MichaelRColton/PSDR/Hardware/Block_Diagram/Block Diagram.png

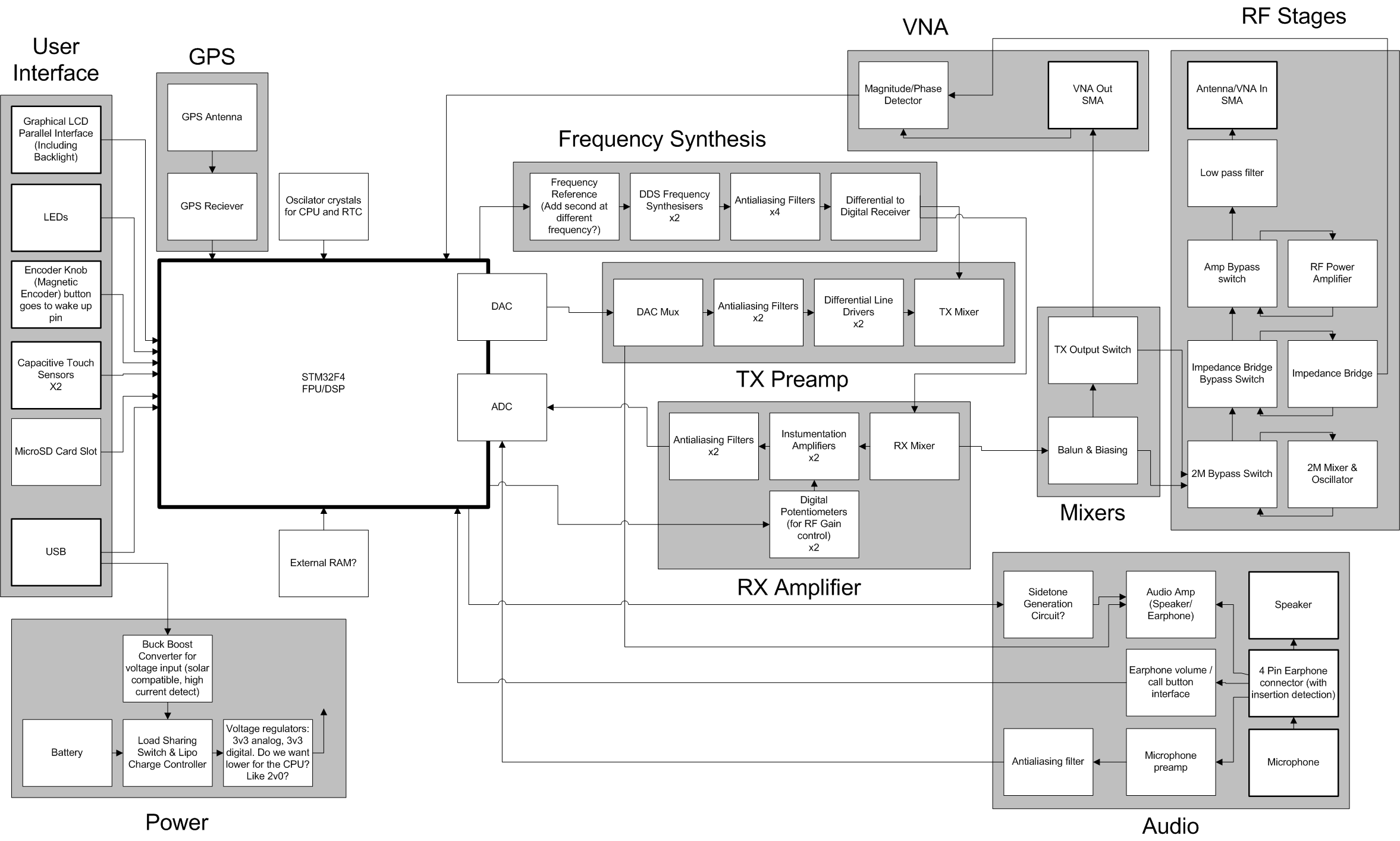
Hardware/Block_Diagram/Block Diagram.png
