MichaelRColton/PSDR/Hardware/Gerbers/PSDR1/bottom.png

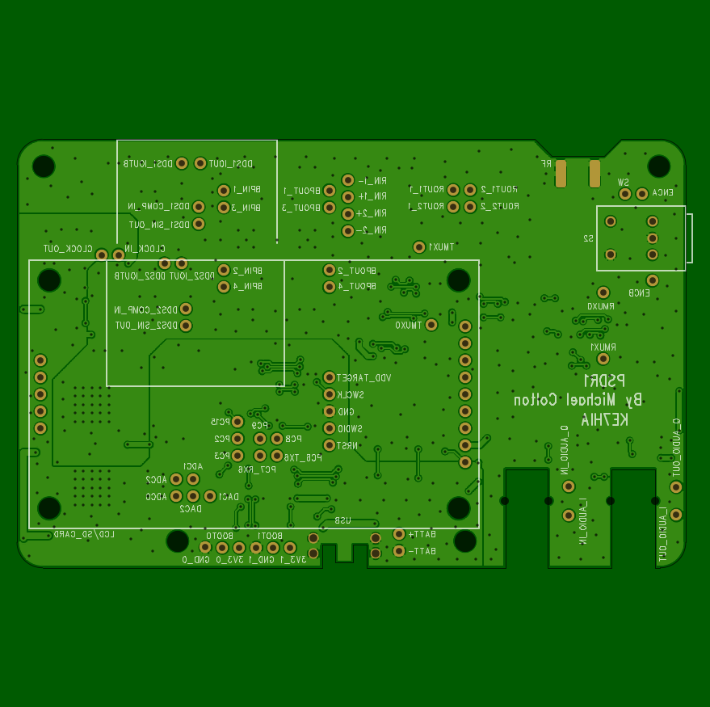
Hardware/Gerbers/PSDR1/bottom.png
