MichaelRColton/PSDR/Hardware/Gerbers/PSDR1/top.png

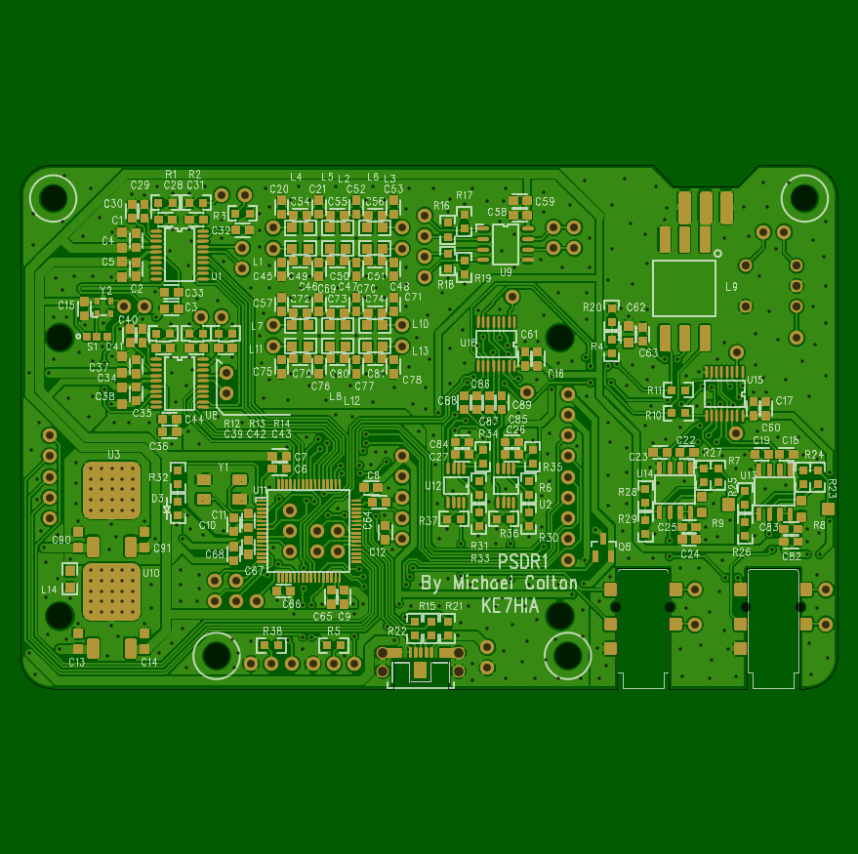
Hardware/Gerbers/PSDR1/top.png
