MichaelRColton/PSDR/Hardware/Gerbers/PSDR2 Encoder Board/BOTTOM.png

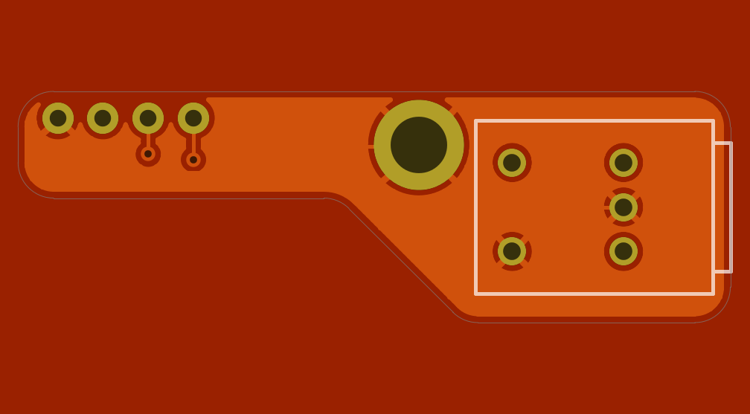
Hardware/Gerbers/PSDR2 Encoder Board/BOTTOM.png
