MichaelRColton/PSDR/Hardware/Gerbers/PSDR2 Encoder Board/TOP.png

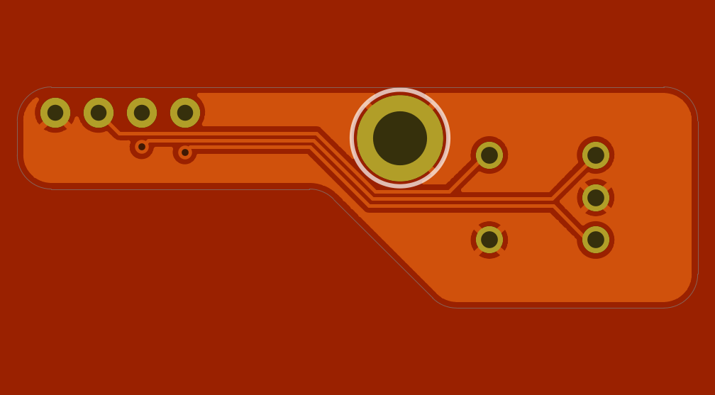
Hardware/Gerbers/PSDR2 Encoder Board/TOP.png
