MichaelRColton/PSDR/Hardware/Gerbers/PSDR2 Main Board/ALL_COPPER.png

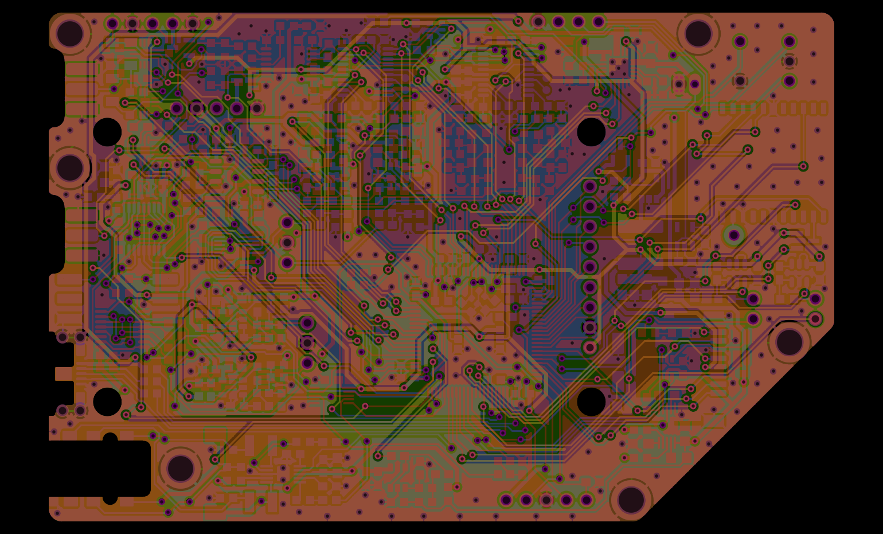
Hardware/Gerbers/PSDR2 Main Board/ALL_COPPER.png
