MichaelRColton/PSDR/Hardware/Gerbers/PSDR2 Main Board/bottom.png

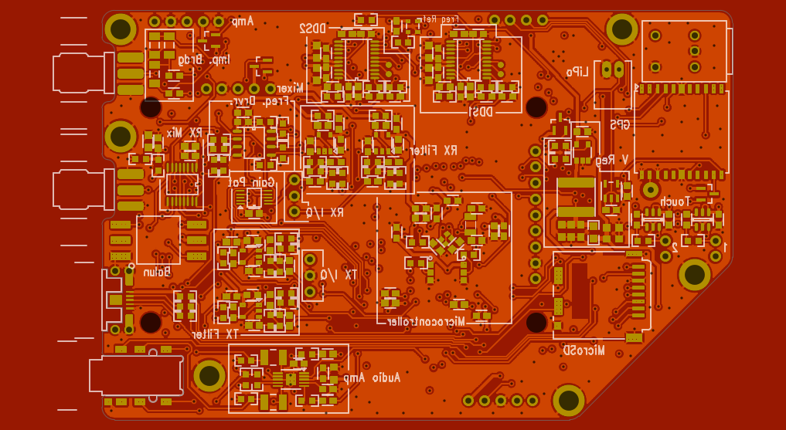
Hardware/Gerbers/PSDR2 Main Board/bottom.png
