MichaelRColton/PSDR/Hardware/Gerbers/PSDR2 Main Board/top.png

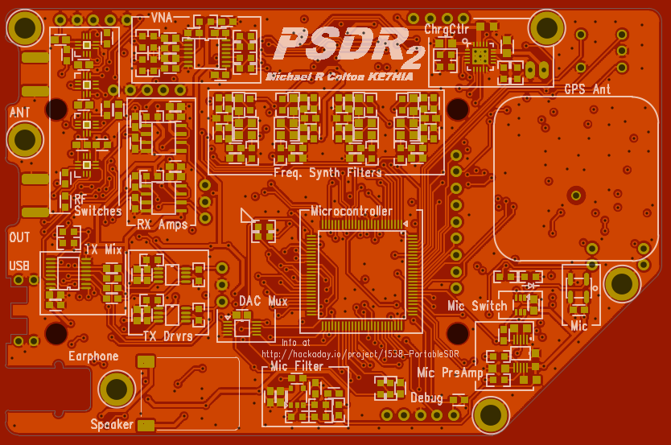
Hardware/Gerbers/PSDR2 Main Board/top.png
