MichaelRColton/PSDR/Hardware/Gerbers/PSDR25 Main Board/TOP.png

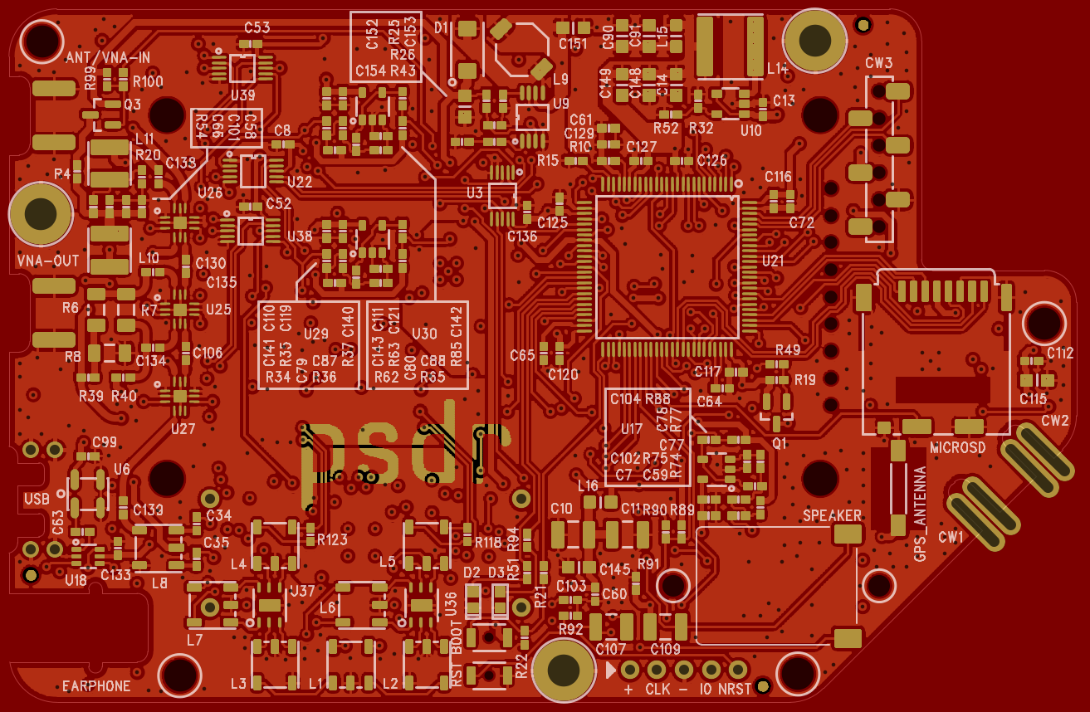
Hardware/Gerbers/PSDR25 Main Board/TOP.png
