MichaelRColton/PSDR/Hardware/Gerbers/PSDR25_Encoder Board/BOTTOM.png

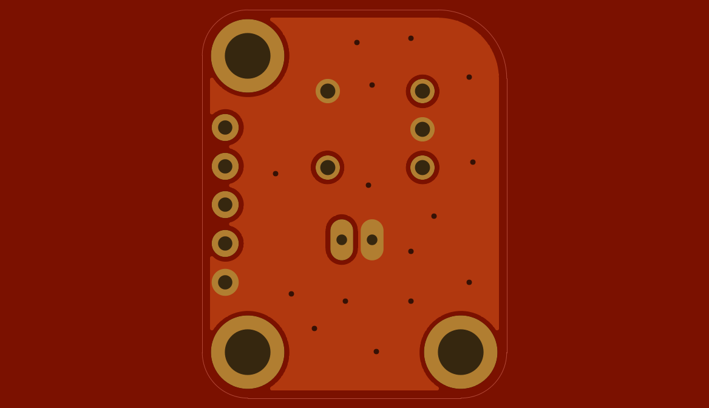
Hardware/Gerbers/PSDR25_Encoder Board/BOTTOM.png
