MichaelRColton/PSDR/Keychain/Gerbers/BOTTOM.png

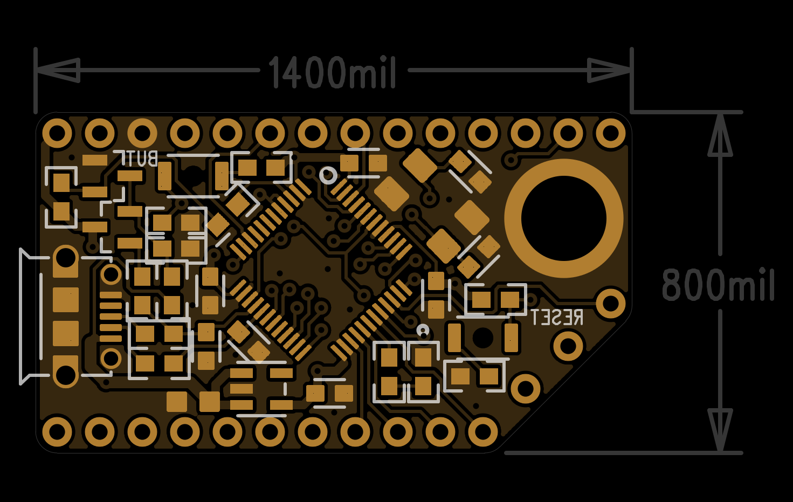
Keychain/Gerbers/BOTTOM.png
