MichaelRColton/PSDR/Keychain/Gerbers/PSDR_Keychain.png

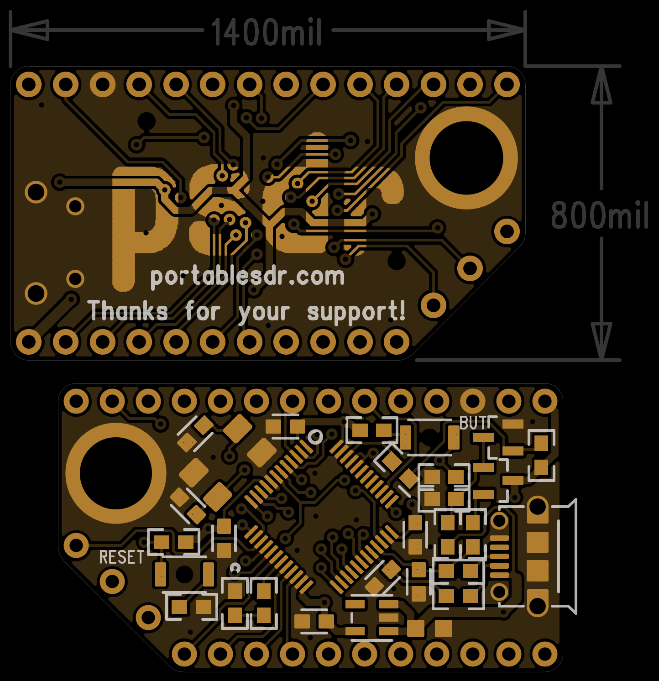
Keychain/Gerbers/PSDR_Keychain.png
