MichaelRColton/PSDR/Keychain/Gerbers/TOP.png

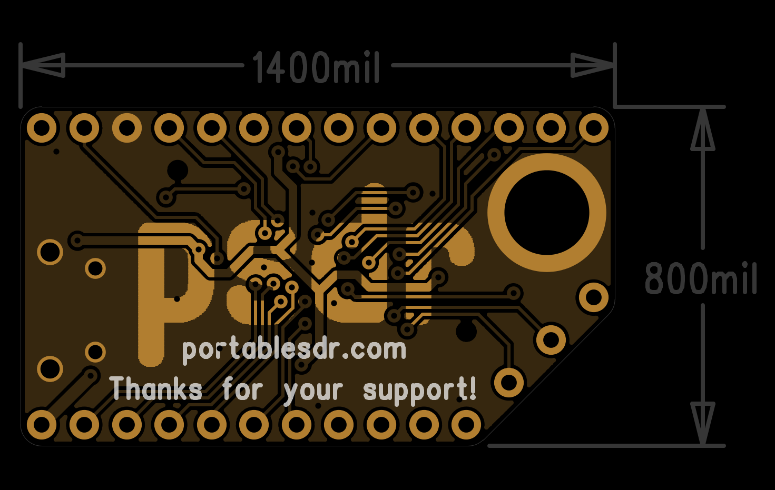
Keychain/Gerbers/TOP.png
