MichaelRColton/PSDR/Hardware/BOMs/PSDR_2.0.0/PSDR2_BOM_Simple.xlsx

RefDes | Count | Part Type | Value | Vendor Part No. | Mfg | Mfg Part No. | Substitutions?
L14 | 1 | 2U2H_INDUCTOR_NR6028T2R2N |  | 587-2098-1-ND | Taiyo Yuden | NR6028T2R2N | Yes
EARPHONE | 1 | 3.5MM_PHONO_4P_3SW_SJ-42617-SMT |  | CP-43617SJCT-ND | CUI Inc | SJ-43617-SMT-TR | No
U11 | 1 | 3V3_LDO_MCP1802 |  | MCP1802T-3302I/OTCT-ND | Microchip Technology | MCP1802T-3302I/OT | No
U15, 16 | 2 | 74CBTLV3253 |  | 568-5265-1-ND | NXP Semiconductors | 74CBTLV3253DS,118 | No
Y2 | 1 | 75MHZ_OSC |  | 535-11201-1-ND | Abracon Corporation | ASDMB-75.000MHZ-LY-T | No
U2, 12 | 2 | AD8131 |  | AD8131ARMZ-ND | Analog Devices Inc | AD8131ARMZ-REEL7 | No
U23 | 1 | AD8302 |  | AD8302ARUZ-ND | Analog Devices Inc | AD8302ARUZ | No
U1, 8 | 2 | AD9834 |  | AD9834CRUZ-ND | Analog Devices Inc | AD9834CRUZ | No
U6 | 1 | ALT-MICROPHONE_MEMS_SPU0410HR5H-PB |  | 423-1138-1-ND | Knowles | SPU0410HR5H-PB | No
U28 | 1 | AUDIO_AMP_TPA0253DGQR |  | 296-7006-1-ND | Texas Instruments | TPA0253DGQR | No
U7 | 1 | BAT-MANAGE_MCP73871 |  | MCP73871-2AAI/ML-ND | Microchip Technology | MCP73871-2AAI/ML | No
U10 | 1 | BUCK_REGULATOR_AP3417C |  | AP3417CKTR-G1DICT-ND | Diodes Incorporated | AP3417CKTR-G1 | No
U19, 20 | 2 | CAP_SENSE_AT42QT1010 |  | AT42QT1011-TSHRCT-ND | Atmel | AT42QT1011-TSHR | No
Y1 | 1 | CRYSTAL_24MHZ_P79E |  | 490-5575-1-ND | Murata Electronics North America | XRCGB24M000F0L00R0 | No
Y5 | 1 | CRYSTAL_SMT_32.768 |  | 535-11937-1-ND | Abracon Corporation | ABS07-120-32.768KHZ-T | No
C9 | 1 | CSM-C0G-100P-5P-50V-0603 | 100p | 1276-1008-1-ND | Samsung Electro-Mechanics America, Inc | CL10C101JB8NNNC | Yes
C68, 111 | 2 | CSM-C0G-100P-5P-50V-0603 | OPEN
C50, 55, 73, 80, 121, 122 | 6 | CSM-C0G-10P-5P-50V-0603 | 6p | 1276-2133-1-ND | Samsung Electro-Mechanics America, Inc | CL10C060CB8NNNC | Yes
C123, 124 | 2 | CSM-C0G-10P-5P-50V-0603 | 8p | 1276-2140-1-ND | Samsung Electro-Mechanics America, Inc | CL10C080DB8NCNC | Yes
C31, 32, 42, 43 | 4 | CSM-C0G-18P-5P-50V-0603 | 18p | 1276-2210-1-ND | Samsung Electro-Mechanics America, Inc | CL10C180JC8NNNC | Yes
C49, 54, 72, 79 | 4 | CSM-C0G-18P-5P-50V-0603 | 1p | 1276-1293-1-ND | Samsung Electro-Mechanics America, Inc | CL10C010CB8NNNC | Yes
C20, 45, 47, 48, 52, 53, 57, 70, 71, 75, 77, 78 | 12 | CSM-C0G-18P-5P-50V-0603 | 22p | 1276-1023-1-ND | Samsung Electro-Mechanics America, Inc | CL10C220JB8NNNC | Yes
C21, 46, 69, 76 | 4 | CSM-C0G-18P-5P-50V-0603 | 33p | 1276-1070-1-ND | Samsung Electro-Mechanics America, Inc | CL10C330JB8NNNC | Yes
C51, 56, 74, 81 | 4 | CSM-C0G-18P-5P-50V-0603 | 5p | 1276-1294-1-ND | Samsung Electro-Mechanics America, Inc | CL10C050CB8NNNC | Yes
C115, 116 | 2 | CSM-C0G-3N3-5P-50V-0603 | 2n2 | 1276-1992-1-ND | Samsung Electro-Mechanics America, Inc | CL10B222KB8SFNC | Yes
C14, 90, 91, 148, 149, 4, 5, 37, 38, 92, 95-98, 145, 84, 85 | 17 | CSM-X5R-10U0-10P-10V-0805 (all but 84,85, close enough) | 10u0 | 1276-1113-1-ND | Samsung Electro-Mechanics America, Inc | CL21B106KQQNNNE | Yes
C86-89 | 4 | CSM-X5R-10U0-20P-6V3-0603 | 22u | 1276-1193-1-ND | Samsung Electro-Mechanics America, Inc | CL10A226MQ8NRNC | Yes
C16, 17, 33, 44, 108, 132, 6, 7, 143 | 9 | CSM-X5R-1U0-10P-25V-0603 | 1u0 | 1276-1946-1-ND | Samsung Electro-Mechanics America, Inc | CL10B105KP8NNNC | Yes
C107, 109 | 2 | CSM-X5R-22U-20P-10V-1210 | 220u | 1276-3375-1-ND | Samsung Electro-Mechanics America, Inc | CL32A227MQVNNNE | Yes
C24, 82, 119, 125 | 4 | CSM-X5R-2U2-10P-6V3-0603 | 2u2 | 1276-1134-1-ND | Samsung Electro-Mechanics America, Inc | CL10B225KP8NNNC | Yes
C62 | 1 | CSM-X5R-47U-20P-6V3-0805 | 47u | 1276-2420-1-ND | Samsung Electro-Mechanics America, Inc | CL21A476MQCLRNC | Yes
C13, 118, 93, 94 | 4 | CSM-X5R-4U7-10P-10V-0603 | 4u7 | 490-3297-1-ND | Murata Electronics North America | GRM188R60J475KE19D | Yes
C105, 110, 144, 146 | 4 | CSM-X5R-4U7-10P-6V3-0603 | 470n | 1276-1062-1-ND | Samsung Electro-Mechanics America, Inc | CL10B474KO8NNNC | Yes
C1-3, 8, 10-12, 25-29, 34-36, 39, 40, 59-61, 63, 83, 99, 104, 106, 112-114, 117, 120, 126-131, 133-142, 147, 150, 155, 156, 161, 162, 167, 168, 173, 174 | 56 | CSM-X7R-100N-10P-25V-0603 | 100n | 490-1532-1-ND | Murata Electronics North America | GRM188R71C104KA01D | Yes
C15, 18, 19, 22, 23, 30, 41, 58, 102, 153, 159, 165, 171 | 13 | CSM-X7R-10N-10P-50V-0603 | 10n | 490-1512-1-ND | Murata Electronics North America | GRM188R71H103KA01D | Yes
C64-67, 100, 101, 151, 152, 157, 158, 163, 164, 169, 170 | 14 | CSM-X7R-1N-10P-50V-0603 | 1n | 490-1494-1-ND | Murata Electronics North America | GRM188R71H102KA01D | Yes
C103, 154, 160, 166, 172 | 5 | CSM-X7R-1U0-10P-10V-0603 | 6u8 | 445-14209-1-ND | TDK Corporation | C1608X6S1A685K080AC | Yes
U22 | 1 | DIGITAL_POT_MAX5388 |  | MAX5388NAUB+-ND | Maxim Integrated | MAX5388NAUB+ | No
U3 | 1 | DPDT_ANALOG_MAX4525 |  | MAX4525CUB+-ND | Maxim Integrated | MAX4525CUB+ | No
U9 | 1 | DS90LV028 |  | DS90LV028AHM/NOPB-ND | Texas Instruments | DS90LV028AHM/NOPB | No
S2 | 1 | ENCODER_PEC09-2320F-S0015 |  | PEC09-2320F-S0015-ND | Bourns Inc. | PEC09-2320F-S0015 | No
U4 | 1 | GP39-1513 |  | GP39-1513 or GP-3363 or one of the new ones. GP39-1513 is the one I liked best for the Gun Box. Let's use that one. | adh-tech.com.tw | GP39-1513 | No (but see note to left)
GPS_ANT | 1 | GPS_CERAMIC_ANT_25X25X2 |  | 535-11938-ND | Abracon Corporation | APAE1575R2520ABDD7-T | Yes, physical match.
L15 | 1 | ISM-0805-10U | 10u | 535-10520-1-ND | Abracon Corporation | AISC-0805F-100J-T | Yes
L2, 3, 5, 6, 8, 10, 12, 13 | 8 | ISM-0805-10U | 390nH | 535-10508-1-ND | Abracon Corporation | AISC-0805-R39J-T | Yes
L1, 4, 7, 11 | 4 | ISM-0805-10U | 470nH | 535-10509-1-ND | Abracon Corporation | AISC-0805-R47J-T | Yes
LIPO | 1 | JST_2P_2MM |  | 455-1719-ND | JST Sales America Inc | S2B-PH-K-S(LF)(SN) | Yes
D3 | 1 | LED-WHITE-0603 | APTD1608QWF | 475-2831-1-ND | OSRAM Opto Semiconductors Inc | LW Q38E-Q1S2-3K6L-1 | Yes
U13, 14 | 2 | MCP6N11 |  | MCP6N11-010E/SN-ND | Microchip Technology | MCP6N11-010E/SN | No | OTHER GAIN OPTIONS EXIST (the -010 part) I should try them.
U5 | 1 | MIC_PREAMP_SSM2167 |  | SSM2167-1RMZ-R7CT-ND | Analog Devices Inc | SSM2167-1RMZ-R7 | No
MICROSD | 1 | MICROSD_DM3CS-SF |  | DM3CS-SF | Hirose Electric Co Ltd | DM3CS-SF | No
USB | 1 | MICROUSB_H12192CT-ND |  | H12192CT-ND | Hirose Electric Co Ltd | ZX62WRD-B-5PC | No
Q1-3, 8 | 4 | MOSFET_P_SOT23_IRLML6401 |  | IRLML6401PBFCT-ND | International Rectifier | IRLML6401TRPBF | Yes
U17, 29-32 | 5 | OP_AMP_FAN4174 |  | FAN4174IS5XCT-ND | Fairchild Semiconductor | FAN4174IS5X | No
LCD | 1 | QVGA_SPI_DISPLAY_MINIMAL |  |  | ebay (also alibaba) |  | Yes | Supplier TBD
U24-27 | 4 | RF_DPDT_MASWSS0129TR |  | 1465-1374-1-ND | M/A-Com Technology Solutions | MASWSS0129TR-3000 | No
R5, 21, 28-31, 33, 55, 78-89 | 20 | RSM-0R0-1PCT-125MW-0603 | 0R0 | 541-0.0GCT-ND | Vishay Dale | CRCW06030000Z0EA | Yes
R49, 50, 56, 57, 60, 64, 65, 68, 69, 72, 73, 76, 77, 90-95 | 19 | RSM-100K-1PCT-100MW-0603 | 100K | P100KGCT-ND | Panasonic Electronic Components | ERJ-3GEYJ104V | Yes
R43 | 1 | RSM-100R-1PCT-100MW-0603 | 100R | P100GCT-ND | Panasonic Electronic Components | ERJ-3GEYJ101V | Yes
R4, 20, 44, 45, 47, 48, 62, 63, 66, 67, 70, 71, 74, 75 | 14 | RSM-10K0-1PCT-100MW-0603 | 10K0 | MCT0603-10.0K-CFCT-ND | Vishay Beyschlag | MCT06030C1002FP500 | Yes
R41 | 1 | RSM-10K0-1PCT-100MW-0603 | 10K0 NTC | 490-2436-1-ND | Murata Electronics North America | NCP18XH103J03RB | Yes
R39 | 1 | RSM-110K-1PCT-100MW-0603 | 110K | P110KGCT-ND | Panasonic Electronic Components | ERJ-3GEYJ114V | Yes
R51, 52, 96, 97 | 4 | RSM-12K1-1PCT-100MW-0603 | 12K1 | 1276-4751-1-ND | Samsung Electro-Mechanics America, Inc | RC1608F1212CS | Yes
R10, 11 | 2 | RSM-150R-1PCT-100MW-0603 | 150R | P150GCT-ND | Panasonic Electronic Components | ERJ-3GEYJ151V | Yes
R38 | 1 | RSM-15K0-1PCT-100MW-0603 | 15K0 | MCT0603-15.0K-CFCT-ND | Vishay Beyschlag | MCT06030C1502FP500 | Yes
R9, 23, 24, 27, 46, 58, 59 | 7 | RSM-1K00-1PCT-100MW-0603 | 1K00 | MCT0603-1.00K-CFCT-ND | Vishay Beyschlag | MCT06030C1001FP500 | Yes
R42 | 1 | RSM-1K30-1PCT-100MW-0603 | 1K30 | 311-1.3KGRCT-ND | Yageo | RC0603JR-071K3L | Yes
R2, 3, 13, 14, 16, 17, 18, 19 | 8 | RSM-200R-1PCT-100MW-0603 | 200R | P200HCT-ND | Panasonic Electronic Components | ERJ-3EKF2000V | Yes
R53, 54 | 2 | RSM-22K1-1PCT-100MW-0603 | 22K1 | P22.1KHCT-ND | Panasonic Electronic Components | ERJ-3EKF2212V | Yes
R15, 22 | 2 | RSM-22R1-1PCT-100MW-0603 | 22R1 | 1276-3497-1-ND | Samsung Electro-Mechanics America, Inc | RC1608F22R1CS | Yes
R34, 35 | 2 | RSM-24R9-1PCT-100MW-0603 | 24R9 | 1276-3499-1-ND | Samsung Electro-Mechanics America, Inc | RC1608F24R9CS | Yes
R32 | 1 | RSM-255R-1PCT-100MW-0603 | 255R | P255HCT-ND | Panasonic Electronic Components | ERJ-3EKF2550V | Yes
R40 | 1 | RSM-332K-1PCT-100MW-0603 | 332K | P332KHCT-ND | Panasonic Electronic Components | ERJ-3EKF3323V | Yes
R61 | 1 | RSM-383K-1PCT-100MW-0603 | 383K | P383KHCT-ND | Panasonic Electronic Components | ERJ-3EKF3833V | Yes
R25, 26, 36, 37 | 4 | RSM-49R9-1PCT-100MW-0603 | 49R9 | 1276-3505-1-ND | Samsung Electro-Mechanics America, Inc | RC1608F49R9CS | Yes
R1, 12 | 2 | RSM-6K81-1PCT-100MW-0603 | 6K81 | P6.81KHCT-ND | Panasonic Electronic Components | ERJ-3EKF6811V | Yes
R6, 7, 8 | 3 | RSM-6K98-1PCT-250MW-1206 | 50R (49R9) | P49.9FCT-ND | Panasonic Electronic Components | ERJ-8ENF49R9V | Yes
ANT/VNA-IN, VNA-OUT | 2 | SMA_BOARD_EDGE |  | J629-ND | Cinch Connectivity Solutions Johnson | 142-0711-821 | Yes (Physical Match Required)
U18 | 1 | SPDT_ANALOG_SWITCH_SN74LVC1G3157 |  | 296-14909-1-ND | Texas Instruments | SN74LVC1G3157DCKR | No
SPEAKER | 1 | SPEAKER_SMT_WATERPROOF_2403-260-00107 |  | 423-1203-ND | Knowles | 2403 260 00107 | Maybe
U21 | 1 | STM32F429_LQFP100 |  | 497-14052-ND | STMicroelectronics | STM32F429VIT6 | Yes, ST, pin compatible, equal or higher specs.
L9 | 1 | T4-1-KK81 |  |  | Mini-Circuits | T4-1-KK81 | No
 | 0.3 | LCD Male Header |  | SAM1000-32-ND | Samtec Inc | BBL-132-G-E | Yes. See below
 | 0.3 | LCD Female Header |  | SAM1104-32-ND | Samtec Inc | BBL-132-G-E | Yes. Must mate with above, stacked height may not change
 | 1.00 | Lipo |  |  | Sparkfun.com | PRT-08483
Number of different parts | 85
Part count | 337.6
