MichaelRColton/PSDR/Hardware/BOMs/PSDR_1.0.0/PSDR1_BOM.xlsx

RefDes | Count | Part Type | Mfg PN | Vendor PN | Manufacturer | Value
C1-3,6,8,9,12,25-29,34-36,39,40,59-61,63,66,67,83 | 24 | CSM-X7R-100N-10P-25V-0603 |  | 490-1532-1-ND |  | 100n
C15,18,19,22,23,30,41,58 | 8 | CSM-X7R-10N-10P-50V-0603 |  | 490-1512-1-ND |  | 10n
C4,5,37,38,13,14,84,85,90,91 | 10 | CSM-X5R-10U0-10P-25V-0805 |  | 1276-1113-1-ND |  | 10u0
C10,11,31,32,42,43 | 6 | CSM-C0G-18P-5P-50V-0603 |  | 1276-2210-1-ND |  | 18p
C49,54,72,79 | 4 | CSM-C0G-18P-5P-50V-0603 |  | 1276-1293-1-ND |  | 1p
C16,17,33,44,68 | 5 | CSM-X5R-1U0-10P-25V-0603 |  | 1276-1946-1-ND |  | 1u0
C20,45,47,48,52,53,57,70,71,75,77,78 | 12 | CSM-C0G-18P-5P-50V-0603 |  | 1276-1023-1-ND |  | 22p
C24,64,65,82 | 4 | CSM-X5R-2U2-10P-6V3-0603 |  | 1276-1134-1-ND |  | 2u2
C21,46,69,76 | 4 | CSM-C0G-18P-5P-50V-0603 |  | 1276-1070-1-ND |  | 33p
C62 | 1 | CSM-X5R-47U-20P-6V3-0805 |  | 1276-2420-1-ND |  | 47u
C7 | 1 | CSM-X5R-4U7-10P-10V-0603 |  | 1276-2087-1-ND |  | 4u7
C51,56,74,81 | 4 | CSM-C0G-18P-5P-50V-0603 |  | 1276-1294-1-ND |  | 5p
C50,55,73,80 | 4 | CSM-C0G-18P-5P-50V-0603 |  | 1276-2133-1-ND |  | 6p
C86-89 | 4 | CSM-X5R-10U0-20P-6V3-0603 |  | 1276-1193-1-ND |  | 22u
R8,9 | 2 | 10K_POT |  | TC33X-103ECT-ND
R21 | 1 | RSM-0R0-1PCT-125MW-0603 |  | 541-0.0GCT-ND |  | 0R0
R7,23 | 2 | RSM-100K-1PCT-100MW-0603 |  | 541-100KHCT-ND |  | 100K
R4,5,20,38 | 4 | RSM-10K0-1PCT-100MW-0603 |  | MCT0603-10.0K-CFCT-ND |  | 10K0
R10,11 | 2 | RSM-150R-1PCT-100MW-0603 |  | 541-150HCT-ND |  | 150R
R6,24-31,33 | 9 | RSM-1K00-1PCT-100MW-0603 |  | MCT0603-1.00K-CFCT-ND |  | 1K00
R2,3,13,14,16-19 | 8 | RSM-200R-1PCT-100MW-0603 |  | 541-200HCT-ND |  | 200R
R15,22 | 2 | RSM-22R1-1PCT-100MW-0603 |  | 541-22.1HCT-ND |  | 22R1
R34,35 | 2 | RSM-24R9-1PCT-100MW-0603 |  | 541-24.9HCT-ND |  | 24R9
R32 | 1 | RSM-255R-1PCT-100MW-0603 |  | 541-255HCT-ND |  | 255R
R36,37 | 2 | RSM-49R9-1PCT-100MW-0603 |  | 541-49.9HCT-ND |  | 49R9
R1,12 | 2 | RSM-6K81-1PCT-100MW-0603 |  | MCT0603-6.80K-CFCT-ND |  | 6K81
L2,3,5,6,8,10,12,13 | 8 | ISM-0805-10U |  | 535-10508-1-ND |  | 390nH
L1,4,7,11 | 4 | ISM-0805-10U |  | 535-10509-1-ND |  | 470nH
L14 | 1 | ISM-0805-10U |  | 535-10520-1-ND |  | 10u
D3 | 1 | LED-WHITE-0603 | VLMW11R2S2-5K8L-08 | VLMW11R2S2-5K8L-08CT-ND
L9 | 1 | T4-1-KK81 | T4-1-KK81+
LCD/SD_CARD | 1 | QVGA_SPI_DISPLAY
Q8 | 1 | MOSFET_P_SOT23_IRLML6401 | IRLML6401TRPBF | IRLML6401PBFCT-ND
RF | 1 | SMA_BOARD_EDGE | 142-0711-821 | J629-ND
RX_I/Q, TX_I/Q | 2 | PHONO_JACK_STEREO_CUTOUT_SWITCHES | SJ-3503-SMT-TR | CP-3503SJCT-ND
S2 | 1 | ENCODER_PEC09-2320F-S0015 | PEC09-2320F-S0015 | PEC09-2320F-S0015-ND
U1,8 | 2 | AD9834 | AD9834CRUZ-ND | AD9834CRUZ-ND
U2,12 | 2 | AD8131 | AD8131 | AD8131ARMZ-ND
U3,10 | 2 | LD39300DT33-R | LD39300DT33-R | 497-6874-1-ND
U9 | 1 | DS90LV028 | DS90LV028AHM/NOPB | DS90LV028AHM/NOPB-ND
U11 | 1 | STM32F415RG | STM32F415RG | 497-11907-ND
U13,14 | 2 | MCP6N11 | MCP6N11-010E/SN-ND | MCP6N11-010E/SN-ND
U15,16 | 2 | 74CBTLV3253 | 74CBTLV3253DS,118 | 568-5265-1-ND
USB | 1 | MICROUSB_H12192CT-ND | ZX62WRD-B-5PC | H12192CT-ND
Y1 | 1 | ABMM2-8.000MHZ-E2-T | ABMM2-8.000MHZ-E2-T | 535-9628-1-ND
Y2 | 1 | 75MHZ_OSC | ASDMB-75.000MHZ-LY-T | 535-11201-1-ND
Grand Count | 71
 | 2 | IC TOUCH SENSOR 1KEY SOT23-6 | AT42QT1011-TSHR | AT42QT1011-TSHRCT-ND | Atmel
 | 2 | 2.2nF Cap
 | 2 | 22k RES
 | 2 | 100nF Cap
 | 1 | CONN HEADER PH SIDE 2POS 2MM |  | 455-1719-ND
 | 1 | IC MCU ARM 2MB FLASH 100LQFP | STM32F429VIT6 | 497-14052-ND
 | 0 | CONN AUDIO JACK 3.5MM 4COND SMD | SJ-43516-SMT-TR | CP-43516SJCT-ND |  |  | 0.338 | watts
 | 1 | CONN JACK 3.5MM R/A 4POS MID SMD | SJ-43617-SMT-TR | CP-43617SJCT-ND
 | 1 | IC REG LDO 3.3V 0.3A SOT23-5 | MCP1802T-3302I/OT | MCP1802T-3302I/OTCT-ND |  |  |  | 2000
 | 1 | IC POT DGTL 256-TAP 10UMAX | MAX5388NAUB+ | MAX5388NAUB+-ND |  |  |  | 15.38461538
 | 4 | DPDT LEAD FREE SWITCH DC - 6GHZ | MASWSS0129TR-3000 | 1465-1374-1-ND
 | 1 | IC AMP AUDIO PWR 1W MONO 10MSOP | TPA0253DGQR | 296-7006-1-ND
 | 2 | CAP CER 220UF 6.3V 20% X5R 1210 |  | 1276-3375-1-ND
 | 1 | IC SWITCH SPDT SC70-6 |  | 296-14909-1-ND |  |  |  | 0.435
 | 1 | IC MULTIPLEXER 2X2 10UMAX |  | MAX4525CUB+-ND |  |  |  | 13.33333333
 | 1 | IC REG BUCK SYNC ADJ 1A SOT25 |  | AP3417CKTR-G1DICT-ND | These are so cheap and small, what's the catch?
 | 1 | INDUCTOR 2.2UH 4.2A 30% SMD |  | 587-2098-1-ND
