MichaelRColton/PSDR/Hardware/BOMs/PSDR_2.6.1/PSDR2.6.1_BOM.xls

 | Yellow is changed from 2.6
 | Red is something to take note of.
Item No. | Ref Des | Qty per unit | Type | Vendor | Vendor Part # | Mfg | Mfg Part # | Value |  | Cost x1 | Cost x10 | Cost x100 | Run Tot x1 | Run Tot x10 | Run Tot x100
1 | -,+,CLK,IO,NRST | 2 | 0.1"_1PIN * 5 for programming header, and encoder board | Digikey | WM50018-05-ND |  |  |  | Only One will be populated per board (give the second one to me) | 0.51 | 0.482 | 0.3693 | 1.02 | 0.964 | 0.7386
2 | ANT/VNA-IN,VNA-OUT | 2 | SMA_BOARD_EDGE | Digikey | J629-ND |  |  |  |  | 7.15 | 6.37 | 4.68 | 14.3 | 12.74 | 9.36
3 | BOOT,RST | 2 | BUTTON_B3U-1000P-B | Digikey | SW1143CT-ND |  |  |  |  | 1.25 | 1.201 | 0.9064 | 2.5 | 2.402 | 1.8128
4 | C3,10,13,17,20,21,26,27,31,33,35,36,38,40,48,49,59,60,71,73,78,80,87,88,96,111,118,119,123,129,139,157,193,209,210,212,217,218,228,229,238-240,242,243,248,256,259,265,267,269,275,277,282-284,289-295,302,303,305,306,317 | 68 | CAP_0603 | Digikey | 490-1532-1-ND |  |  | 100N |  | 0.1 | 0.019 | 0.0086 | 6.8 | 1.292 | 0.5848
5 | C9,278,281,316 | 4 | CAP_0603 | Digikey | 1276-1008-1-ND |  |  | 100p |  | 0.1 | 0.025 | 0.0116 | 0.4 | 0.1 | 0.0464
6 | C46,57,135,215,226 | 5 | CAP_0603 | Digikey | 490-1512-1-ND |  |  | 10N |  | 0.1 | 0.019 | 0.0085 | 0.5 | 0.095 | 0.0425
7 | C83,89,103,104,106-108,147,155,156,188,191,192,247,258 | 15 | CAP_0805 | Digikey | 1276-1113-1-ND |  |  | 10u |  | 0.27 | 0.183 | 0.0932 | 4.05 | 2.745 | 1.398
8 | C8,51,54,62,65,132,134,220,223,231,235,309,315,318,322 | 15 | CAP_0603 | Digikey | 490-1494-1-ND |  |  | 1N |  | 0.1 | 0.02 | 0.0091 | 1.5 | 0.3 | 0.1365
9 | C110,148,149,171,173,213,288 | 7 | CAP_0603 | Digikey | 1276-1946-1-ND |  |  | 1U |  | 0.1 | 0.041 | 0.0187 | 0.7 | 0.287 | 0.1309
10 | C42,43,142,143,151,152,154,158,163,323,326 | 11 | CSM-X5R-22U-20P-10V-1210 | Digikey | 1276-3375-1-ND |  |  | 220u | Do I really want to use these? They cost a lot! | 1.65 | 1.351 | 0.9558 | 18.15 | 14.861 | 10.5138
11 | C251,252,262,263 | 4 | CAP_0603 | Digikey | 1276-1193-1-ND |  |  | 22U | REALLY?!!, if I can get 22U in an 0603 why am I bothering with 0805s for 10u? | 0.25 | 0.205 | 0.1024 | 1 | 0.82 | 0.4096
12 | C186 | 0 | CAP_0603 | Digikey | 1276-1084-1-ND |  |  | 2p2 |  | 0.1 | 0.037 | 0.017 | 0 | 0 | 0
13 | C7,95,125,257,276 | 5 | CAP_0603 | Digikey | 1276-1134-1-ND |  |  | 2U2 |  | 0.17 | 0.115 | 0.0546 | 0.85 | 0.575 | 0.273
14 | C93 | 1 | CAP_0603 | Digikey | 1276-2030-1-ND |  |  | 3300pF |  | 0.1 | 0.036 | 0.0165 | 0.1 | 0.036 | 0.0165
15 | C91 | 1 | CAP_0603 | Digikey | 490-12541-1-ND |  |  | 33nF |  | 0.1 | 0.071 | 0.0325 | 0.1 | 0.071 | 0.0325
16 | C195,197,203,205 | 4 | CAP_0603 | Digikey | 1276-1062-1-ND |  |  | 470N |  | 0.1 | 0.066 | 0.0303 | 0.4 | 0.264 | 0.1212
17 | C301 | 1 | CSM-X5R-47U-20P-6V3-0805 | Digikey | 1276-2420-1-ND |  |  | 47u |  | 0.77 | 0.737 | 0.3575 | 0.77 | 0.737 | 0.3575
18 | C115,120,159,160 | 4 | CAP_0603 | Digikey | 490-3297-1-ND |  |  | 4U7 |  | 0.11 | 0.078 | 0.0358 | 0.44 | 0.312 | 0.1432
19 | C179,184 | 2 | CAP_0603 | Digikey | 1276-2133-1-ND |  |  | 6P |  | 0.1 | 0.042 | 0.0193 | 0.2 | 0.084 | 0.0386
20 | C45,56,137,214,225 | 5 | CAP_0603 | Digikey | 445-14209-1-ND |  |  | 6U8 |  | 0.48 | 0.42 | 0.21 | 2.4 | 2.1 | 1.05
21 | C180,181 | 2 | CAP_0603 | Digikey | 1276-2140-1-ND |  |  | 8P |  | 0.1 | 0.042 | 0.0193 | 0.2 | 0.084 | 0.0386
22 | C307,320 | 2 | CAP_0603 | Digikey | NA |  |  | OPEN |  |  |  |  | 0 | 0 | 0
23 | D100 | 1 | LED_0603 WHITE | Digikey | 475-2831-1-ND |  |  |  |  | 0.35 | 0.256 | 0.167 | 0.35 | 0.256 | 0.167
24 | D101 | 1 | LED_0603 RED | Digikey | 475-2512-1-ND |  |  |  |  | 0.27 | 0.198 | 0.1044 | 0.27 | 0.198 | 0.1044
25 | D102 | 1 | LED_0603 ORANGE | Digikey | 511-1577-1-ND (https://www.digikey.com/product-detail/en/rohm-semiconductor/SML-D12D8WT86/511-1577-1-ND/1641809) |  |  |  |  | 0.34 | 0.264 | 0.144 | 0.34 | 0.264 | 0.144
26 | D44 | 1 | DIODE-SMA | Digikey | MBRA340T3GOSCT-ND |  |  |  |  | 0.46 | 0.394 | 0.2939 | 0.46 | 0.394 | 0.2939
27 | EARPHONE | 1 | 3.5MM_PHONO_4P_3SW_SJ-42617-SMT | Digikey | CP-43617SJCT-ND |  |  |  | Buy but do not populate | 1.86 | 1.443 | 1.1011 | 1.86 | 1.443 | 1.1011
28 | GPS_ANTENNA | 1 | GPS_ANTENNA-W3062A | Digikey | 553-2579-1-ND | Pulse Electronics Corporation | W3062A |  |  | 1.7 | 1.499 | 1.1844 | 1.7 | 1.499 | 1.1844
29 | J153 | 1 | 0.1"_6P_HEADER_DUAL_ENTRY_1241152-6 | Digikey | A107015CT-ND |  |  |  |  | 2.43 | 2.19 | 1.87 | 2.43 | 2.19 | 1.87
30 | J170 | 1 | SPI_LCD_BOTTOM_ENTRY | Digikey | A107013CT-ND |  |  |  |  | 2.42 | 2.26 | 1.96 | 2.42 | 2.26 | 1.96
31 | L34,105,141 | 3 | ISM-0805-10U | Digikey | 445-173012-1-ND (https://www.digikey.com/product-detail/en/tdk-corporation/VLS201612HBX-2R2M-1/445-173012-1-ND/5250931) |  |  | 10u |  | 0.33 | 0.293 | 0.2113 | 0.99 | 0.879 | 0.6339
32 | L109 | 1 | 2U2H_INDUCTOR_NR6028T2R2N | Digikey | 587-2098-1-ND |  |  |  |  | 0.35 | 0.311 | 0.2243 | 0.35 | 0.311 | 0.2243
33 | L39,82 | 2 | BALUN_1-2_WBC2-1TL | Coilcraft | WBC2-1TLB |  |  |  |  | 3.45 | 3.45 | 3.45 | 6.9 | 6.9 | 6.9
34 | L84 | 1 | IND_4.7UH_SMT_CDRH4D28CNP-4R7PC | Digikey | 308-2043-1-ND | Sumida America Components Inc. | CDRH4D28CNP-4R7PC |  |  | 0.87 | 0.763 | 0.6582 | 0.87 | 0.763 | 0.6582
35 | L11,19 | 2 | IND_SMT_220UH_SRN4018-221M | Digikey | SRN4018-221MCT-ND | Bourns Inc. | SRN4018-221M |  |  | 0.36 | 0.32 | 0.24 | 0.72 | 0.64 | 0.48
36 | L41,81 | 2 | MIXER_DIODE-RING_ADE-2ASK | Mini-Circuits | ADE-2ASK |  |  |  |  | 5.55 | 5.55 | 4.15 | 11.1 | 11.1 | 8.3
37 | MICROSD | 1 | MICROSD_DM3CS-SF | Digikey | HR1972CT-ND |  |  |  |  | 1.66 | 1.509 | 1.2936 | 1.66 | 1.509 | 1.2936
38 | Q5,126,178,208,246 | 5 | MOSFET_P_SOT23_IRLML6401 | Digikey | IRLML6401PBFCT-ND |  |  |  |  | 0.36 | 0.295 | 0.2013 | 1.8 | 1.475 | 1.0065
39 | R68,69,75,76,117,169,310-313,319 | 11 | RES_0603 | Digikey | 541-0.0GCT-ND |  |  | 0R |  | 0.1 | 0.022 | 0.0091 | 1.1 | 0.242 | 0.1001
40 | R1,52,53,63,64,112,124,130,140,144,145,165,174-176,207,221,222,232,234,245,285,286,296,297 | 25 | RES_0603 | Digikey | P100KGCT-ND |  |  | 100k |  | 0.1 | 0.1 | 0.0071 | 2.5 | 2.5 | 0.1775
41 | R6,14,268 | 1 | RES_0603 | Digikey | P100GCT-ND |  |  | 100R |  | 0.1 | 0.1 | 0.0071 | 0.1 | 0.1 | 0.0071
42 | R14 | 1 | RES_0603 | Digikey | RHM68DCT-ND (http://www.digikey.com/product-detail/en/rohm-semiconductor/ESR03EZPJ680/RHM68DCT-ND/4053812) |  |  | 68R |  | 0.1 | 0.079 | 0.0303 | 0.1 | 0.079 | 0.0303
43 | R6 | 1 | RES_0603 | Digikey | RHM180DCT-ND (http://www.digikey.com/product-detail/en/rohm-semiconductor/ESR03EZPJ181/RHM180DCT-ND/1983784) |  |  | 180R |  | 0.1 | 0.079 | 0.0303 | 0.1 | 0.079 | 0.0303
44 | R50,55,61,66,92,116,127,133,136,219,224,230,236,299,300 | 15 | RES_0603 | Digikey | MCT0603-10.0K-CFCT-ND |  |  | 10K |  | 0.17 | 0.145 | 0.0568 | 2.55 | 2.175 | 0.852
45 | R168 | 1 | RES_0603 | Digikey | 490-2436-1-ND |  |  | 10K NTC |  | 0.2 | 0.169 | 0.1067 | 0.2 | 0.169 | 0.1067
46 | R12 | 1 | RES_0603 | Digikey | RHM10DCT-ND |  |  | 10R 1/4W |  | 0.1 | 0.079 | 0.0303 | 0.1 | 0.079 | 0.0303
47 | R194,196,198,204 | 4 | RES_0603 | Digikey | 1276-4751-1-ND |  |  | 12K1 |  | 0.1 | 0.014 | 0.0057 | 0.4 | 0.056 | 0.0228
48 | R190 | 1 | RES_0603 | Digikey | MCT0603-15.0K-CFCT-ND |  |  | 15K |  | 0.17 | 0.145 | 0.0568 | 0.17 | 0.145 | 0.0568
49 | R2,28,29,67,70,74,77,122,128,146,150,162,167,177,200-202,206,244,250,254,264,266,270,271,273,274 | 27 | RES_0603 | Digikey | MCT0603-1.00K-CFCT-ND |  |  | 1K |  | 0.17 | 0.145 | 0.0568 | 4.59 | 3.915 | 1.5336
50 | R324,325 | 2 | RES_0603 | Digikey | 1276-3497-1-ND |  |  | 22R1 |  | 0.1 | 0.014 | 0.0057 | 0.2 | 0.028 | 0.0114
51 | R249,261, | 2 | RES_0603 | Digikey | 1276-3499-1-ND |  |  | 24R9 |  | 0.1 | 0.014 | 0.0057 | 0.2 | 0.028 | 0.0114
52 | R97,-99 | 3 | RES_0603 | Digikey | P255HCT-ND |  |  | 255R |  | 0.1 | 0.1 | 0.0084 | 0.3 | 0.3 | 0.0252
53 | R164 | 1 | RES_0603 | Digikey | 1276-4870-1-ND (http://www.digikey.com/product-detail/en/samsung-electro-mechanics-america-inc/RC1608F244CS/1276-4870-1-ND/3967842) |  |  | 240K |  | 0.1 | 0.03 | 0.0123 | 0.1 | 0.03 | 0.0123
54 | R90 | 1 | RES_0603 | Digikey | 541-30.0KHCT-ND |  |  | 30K |  | 0.1 | 0.03 | 0.0123 | 0.1 | 0.03 | 0.0123
55 | R113 | 1 | RES_0603 | Digikey | 311-402KHRCT-ND (https://www.digikey.com/product-detail/en/yageo/RC0603FR-07402KL/311-402KHRCT-ND/730170) |  |  | 402K |  | 0.1 | 0.014 | 0.0057 | 0.1 | 0.014 | 0.0057
56 | R308,321 | 2 | RES_0603 | Digikey | 1276-3505-1-ND |  |  | 50R |  | 0.1 | 0.014 | 0.0057 | 0.2 | 0.028 | 0.0114
57 | R22,23,25 | 3 | RSM-6K98-1PCT-250MW-1206 | Digikey | 1276-5659-1-ND |  |  | 50R |  | 0.1 | 0.033 | 0.0136 | 0.3 | 0.099 | 0.0408
58 | R187 | 1 | RES_0603 | Digikey | 541-4.99KHCT-ND |  |  | 5K |  | 0.1 | 0.03 | 0.0123 | 0.1 | 0.03 | 0.0123
59 | R94 | 1 | RES_0603 | Digikey | P6.81KHCT-ND |  |  | 6.8K |  | 0.1 | 0.1 | 0.0084 | 0.1 | 0.1 | 0.0084
60 | R72,79 | 2 | RES_0603 | Digikey | NA |  |  | DNS |  |  |  |  | 0 | 0 | 0
61 | SPEAKER | 0 | SPEAKER_SMT_WATERPROOF_2403-260-00107 | Digikey | AS01508AO-3-R |  |  |  |  | 3.75 | 3 | 2.475 | 0 | 0 | 0
62 | SPEAKER | 1 | SPEAKER_SMT_WATERPROOF_2403-260-00107 | Digikey | 668-1513-ND |  |  |  | Buy but do not populate | 3.13 | 2.5 | 2.0625 | 3.13 | 2.5 | 2.0625
63 | U172 | 1 | 3V3_LDO_MCP1802 | Digikey | MCP1802T-3302I/OTCT-ND |  |  |  |  | 0.53 | 0.53 | 0.4 | 0.53 | 0.53 | 0.4
64 | U211,298 | 2 | 74CBTLV3253 | Digikey | 296-17283-1-ND |  |  |  | Name mismatch is okay, The Digikey part # is the correct part | 1.05 | 0.936 | 0.73 | 2.1 | 1.872 | 1.46
65 | U253,260 | 2 | AD8131 | Digikey | AD8131ARMZ-ND |  |  |  |  | 4.83 | 4.83 | 3.5553 | 9.66 | 9.66 | 7.1106
66 | U314 | 1 | AD8302 | Digikey | AD8302ARUZ-ND |  |  |  |  | 24.86 | 22.926 | 19.5772 | 24.86 | 22.926 | 19.5772
67 | U199 | 1 | AUDIO_AMP_TPA0253DGQR | Digikey | 296-7006-1-ND |  |  |  |  | 1.74 | 1.562 | 1.2527 | 1.74 | 1.562 | 1.2527
68 | U161 | 1 | BAT-MANAGE_MCP73871 | Digikey | MCP73871-2AAI/ML-ND |  |  |  |  | 1.79 | 1.79 | 1.35 | 1.79 | 1.79 | 1.35
69 | U85 | 1 | BOOST_REG_ADP1613 | Digikey | ADP1613ARMZ-R7CT-ND | Analog Devices Inc. | ADP1613ARMZ-R7 |  |  | 2.07 | 1.863 | 1.4947 | 2.07 | 1.863 | 1.4947
70 | U114 | 1 | BUCK_REGULATOR_AP3417C | Digikey | AP3417CKTR-G1DICT-ND |  |  |  |  | 0.41 | 0.348 | 0.2601 | 0.41 | 0.348 | 0.2601
71 | U15 | 1 | DIGITAL_POT_MAX5388 | Digikey | MAX5388NAUB+-ND |  |  |  |  | 1.11 | 1.055 | 1.0456 | 1.11 | 1.055 | 1.0456
72 | U4,18,86 | 3 | DPDT_ANALOG_MAX4525 | Digikey | MAX4525CUB+-ND |  |  |  |  | 2.29 | 2.176 | 2.0018 | 6.87 | 6.528 | 6.0054
73 | U185 | 1 | GPS_MODULE_RXM-GPS-RM-T | Digikey | RXM-GPS-RM-TCT-ND |  |  |  |  | 20.38 | 20.38 | 15.262 | 20.38 | 20.38 | 15.262
74 | U255,272 | 2 | MCP6N11 | Digikey | MCP6N11-010E/SN-ND |  |  |  |  | 1.35 | 1.35 | 1.02 | 2.7 | 2.7 | 2.04
75 | U189 | 1 | MIC_PREAMP_SSM2167 | Digikey | SSM2167-1RMZ-R7CT-ND |  |  |  |  | 2.77 | 2.484 | 2.0381 | 2.77 | 2.484 | 2.0381
76 | U32 | 1 | MICROPHONE_MEMS_SPU0410HR5H-PB | Digikey | 423-1138-1-ND |  |  |  |  | 0.86 | 0.739 | 0.462 | 0.86 | 0.739 | 0.462
77 | U304 | 1 | MMIC-AMP_HMC482ST | Digikey | 599-1068-1-ND (https://www.digikey.com/product-detail/en/rfmd/SXB-2089Z/599-1068-1-ND/937042) |  |  |  | Name mismatch is okay, The Digikey part # is the correct part | 6.13 | 5.495 | 4.4943 | 6.13 | 5.495 | 4.4943
78 | U47,58,131,216,227 | 5 | OP_AMP_FAN4174 | Digikey | FAN4174IS5XCT-ND |  |  |  |  | 0.5 | 0.426 | 0.3179 | 2.5 | 2.13 | 1.5895
79 | U16,24,30 | 3 | RF_DPDT_MASWSS0129TR | Digikey | 1465-1374-1-ND |  |  |  |  | 1.63 | 1.469 | 1.1832 | 4.89 | 4.407 | 3.5496
80 | U241 | 1 | SI5338 | Digikey | 336-2552-ND |  |  |  |  | 14.79 | 14.79 | 13.6902 | 14.79 | 14.79 | 13.6902
81 | U37 | 1 | SPDT_ANALOG_SWITCH_SN74LVC1G3157 | Digikey | 296-14909-1-ND |  |  |  |  | 0.36 | 0.29 | 0.198 | 0.36 | 0.29 | 0.198
82 | U121 | 1 | STM32F746_LQFP100 | Digikey | 497-15819-ND (https://www.digikey.com/product-detail/en/stmicroelectronics/STM32F746VGT6/497-15819-ND/5287178) |  |  |  |  | 16.75 | 15.39 | 12.9976 | 16.75 | 15.39 | 12.9976
83 | U279,280 | 2 | SY10EP52V | Digikey | 576-2520-ND | Microchip Technology | SY10EP52VKG |  |  | 4.49 | 4.49 | 3.4 | 8.98 | 8.98 | 6.8
84 | U287 | 1 | VARIABLE_FILTER_HMC1023 | Digikey | 1127-1662-ND |  |  |  |  | 30.32 | 27.964 | 23.8792 | 30.32 | 27.964 | 23.8792
85 | USB | 1 | MICROUSB_H12192CT-ND | Digikey | H12192CT-ND |  |  |  |  | 1.37 | 1.206 | 1.0406 | 1.37 | 1.206 | 1.0406
86 | Y182,237 | 2 | CRYSTAL3225 | Digikey | SER3627CT-ND |  |  |  |  | 0.63 | 0.526 | 0.42 | 1.26 | 1.052 | 0.84
87 | Y183 | 1 | CRYSTAL_SMT_32.768 | Digikey | 535-11937-1-ND |  |  |  |  | 0.71 | 0.632 | 0.522 | 0.71 | 0.632 | 0.522
88 | Battery connector | 1 |  | Digikey | 455-1719-ND |  |  |  | Buy but do not populate | 0.17 | 0.161 | 0.0991 | 0.17 | 0.161 | 0.0991
89 | Encoder | 1 |  | Digikey | PEC09-2320F-S0015-ND |  |  |  | Buy but do not populate | 3.36 | 3.132 | 2.146 | 3.36 | 3.132 | 2.146
 |  |  |  |  |  |  |  |  |  |  |  |  | Total x1 | Total x10 | Total x100
 |  |  |  |  |  |  |  |  |  |  |  |  | 276.78 | 245.742 | 190.332
