MichaelRColton/PSDR/Hardware/Enclosure/LeeSpring-LTR028E01S.SLDPRT

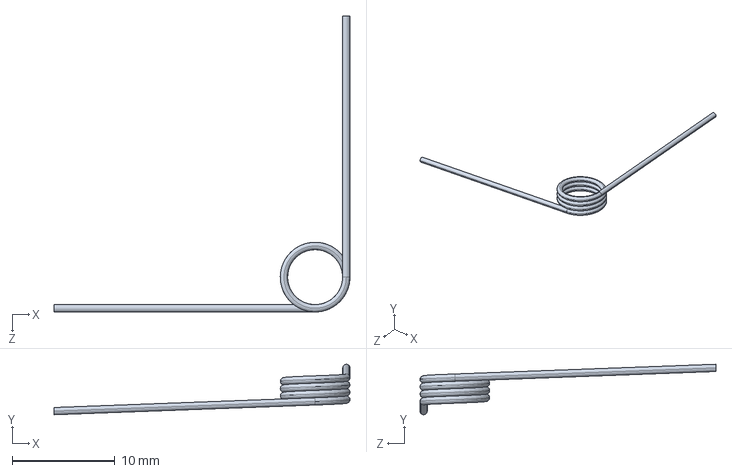
[picture p34: CAD file, 2015-11-12]
Hardware/Enclosure/LeeSpring-LTR028E01S.SLDPRT
28.8 x 4.91 x 28.8 mm
