MichaelRColton/PSDR/Hardware/Enclosure/Bottom_Enclosure.SLDPRT

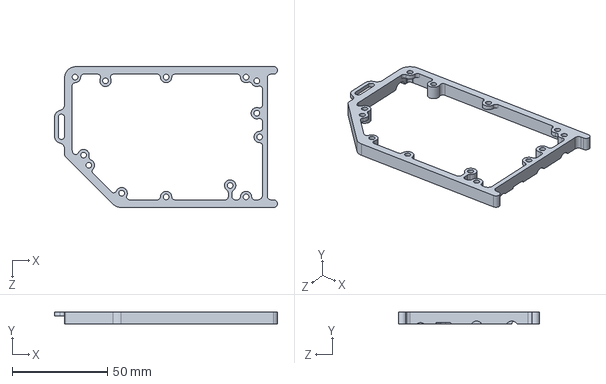
[picture p35: CAD file, 2015-11-12]
Hardware/Enclosure/Bottom_Enclosure.SLDPRT
117.1 x 6.35 x 74.0 mm
