MichaelRColton/PSDR/Hardware/Enclosure/paddle_Mirrored.SLDPRT

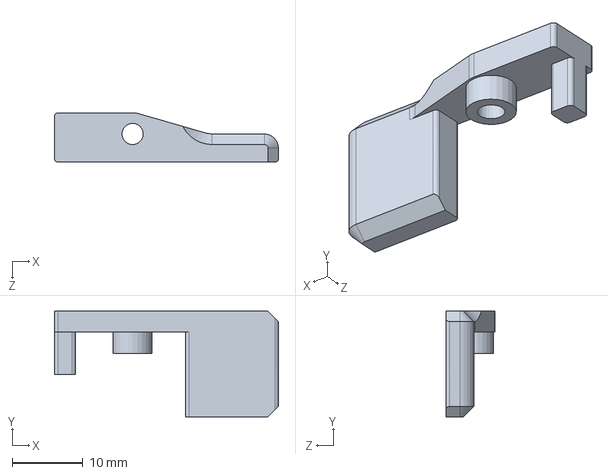
[picture p36: CAD file, 2015-11-12]
Hardware/Enclosure/paddle_Mirrored.SLDPRT
31.7 x 15.0 x 7.00 mm
