MichaelRColton/PSDR/Hardware/Enclosure/GPS_Antenna_18x18x4.SLDPRT

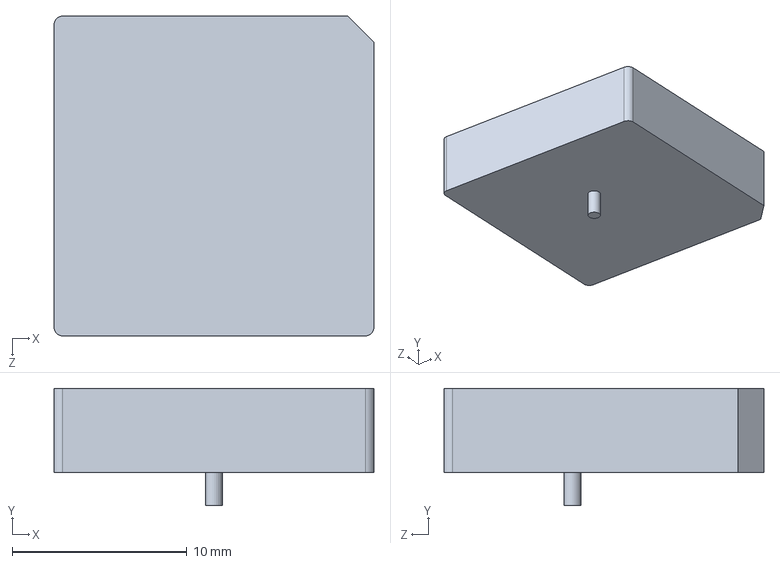
[picture p37: CAD file, 2015-11-12]
Hardware/Enclosure/GPS_Antenna_18x18x4.SLDPRT
18.3 x 6.70 x 18.3 mm
