MichaelRColton/PSDR/Hardware/Enclosure/Top_Cover.SLDPRT

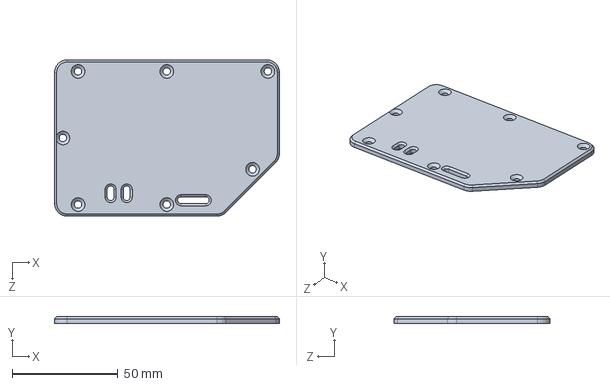
[picture p38: CAD file, 2015-11-12]
Hardware/Enclosure/Top_Cover.SLDPRT
106.5 x 3.17 x 74.0 mm
