MichaelRColton/PSDR/Hardware/Enclosure/LCD_Standoff.SLDPRT

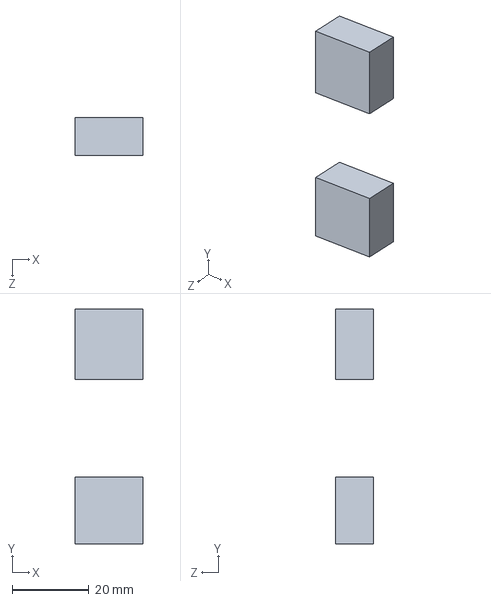
[picture p39: CAD file, 2015-11-12]
Hardware/Enclosure/LCD_Standoff.SLDPRT
17.7 x 61.2 x 10.0 mm
