MichaelRColton/PSDR/Hardware/Enclosure/TopHalf2.sldprt

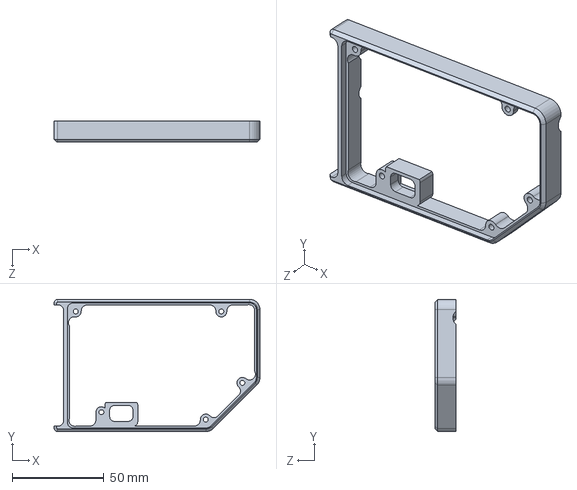
[picture p40: CAD file, 2015-11-12]
Hardware/Enclosure/TopHalf2.sldprt
112.5 x 72.2 x 11.5 mm
