MichaelRColton/PSDR/Hardware/Enclosure/Battery.SLDPRT

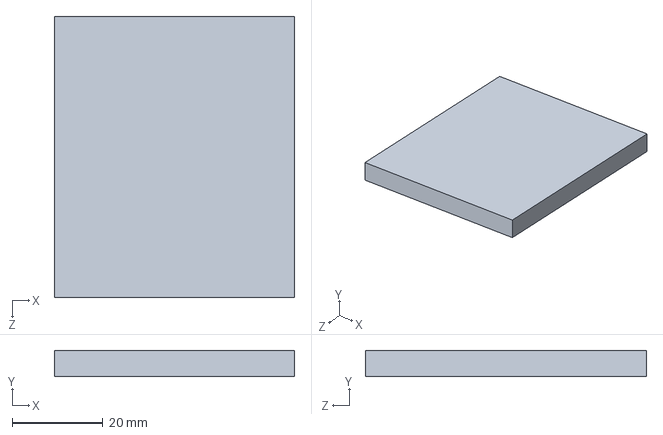
[picture p41: CAD file, 2015-11-12]
Hardware/Enclosure/Battery.SLDPRT
53.0 x 5.75 x 62.0 mm
