MichaelRColton/PSDR/Hardware/Enclosure/Spring Thing.SLDPRT

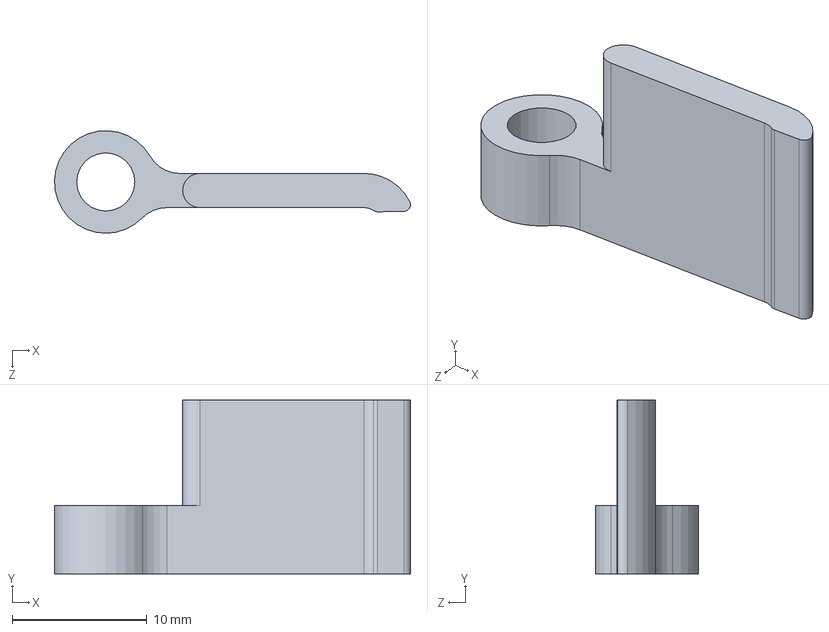
[picture p42: CAD file, 2015-11-12]
Hardware/Enclosure/Spring Thing.SLDPRT
26.4 x 12.9 x 7.62 mm
