MichaelRColton/PSDR/Hardware/Enclosure/LeeSpring-LTL015B08S.SLDPRT

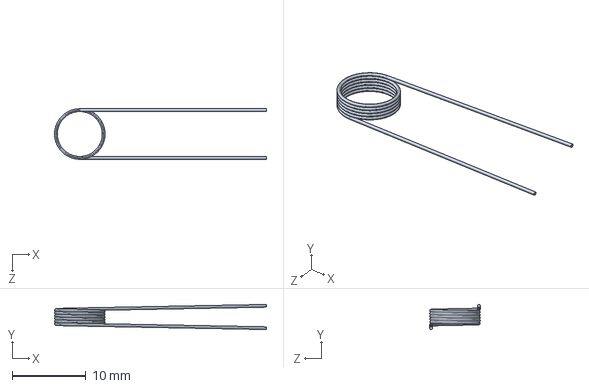
[picture p43: CAD file, 2015-11-12]
Hardware/Enclosure/LeeSpring-LTL015B08S.SLDPRT
28.8 x 3.42 x 6.88 mm
