MichaelRColton/PSDR/Hardware/Enclosure/Knurled_Knob.SLDPRT

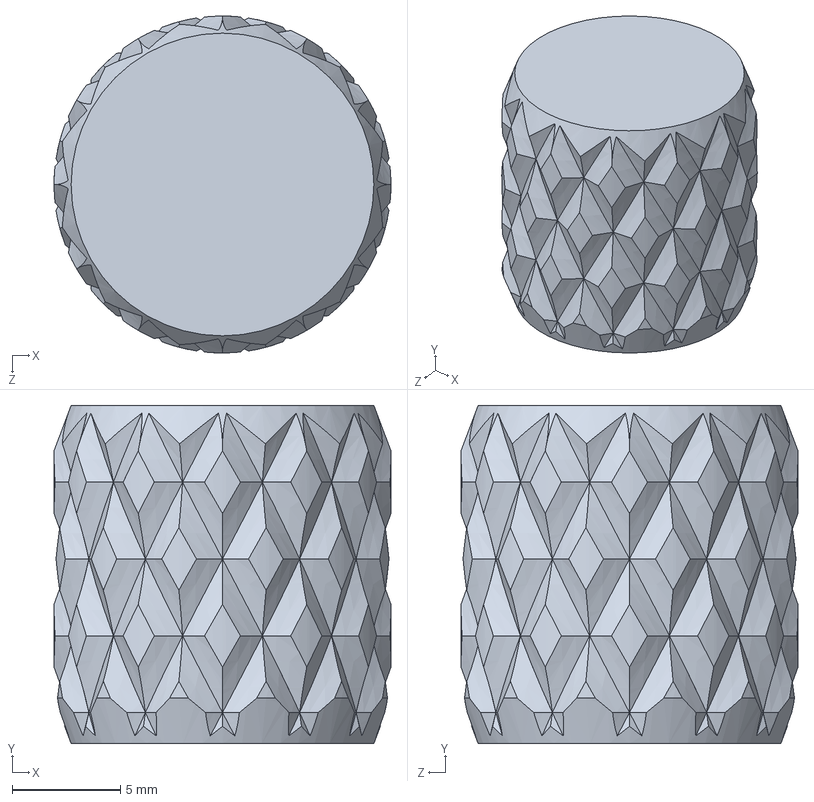
[picture p44: CAD file, 2015-11-12]
Hardware/Enclosure/Knurled_Knob.SLDPRT
15.5 x 15.6 x 15.5 mm
