MichaelRColton/PSDR/Hardware/Enclosure/Encoder.SLDPRT

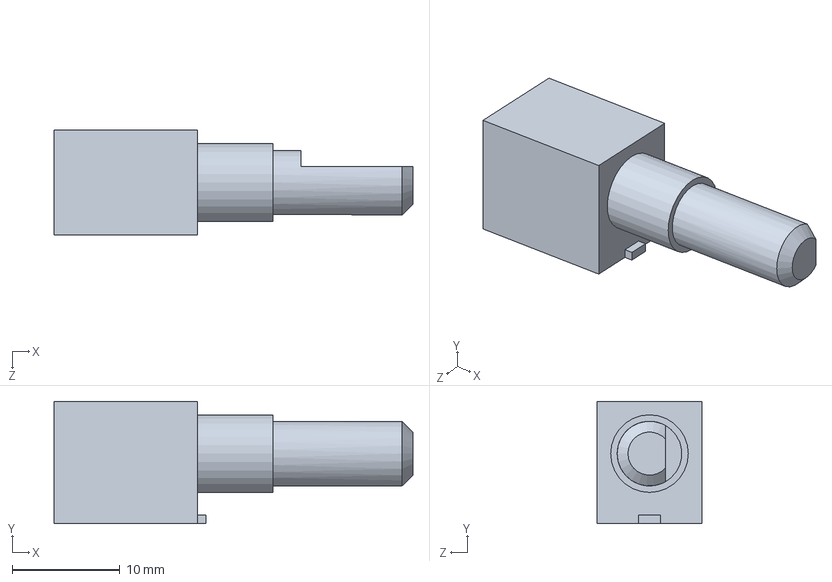
[picture p45: CAD file, 2015-11-12]
Hardware/Enclosure/Encoder.SLDPRT
33.3 x 11.4 x 9.70 mm
