MichaelRColton/PSDR/Hardware/Enclosure/USB_Connector.SLDPRT

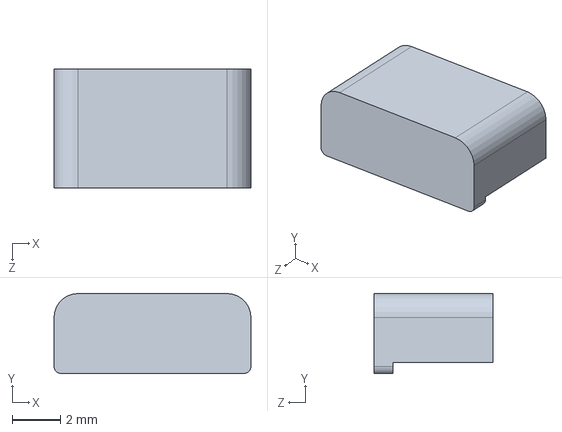
[picture p46: CAD file, 2015-11-12]
Hardware/Enclosure/USB_Connector.SLDPRT
8.20 x 3.33 x 4.93 mm
