MichaelRColton/PSDR/Hardware/Enclosure/Slotted_Knob1.SLDPRT

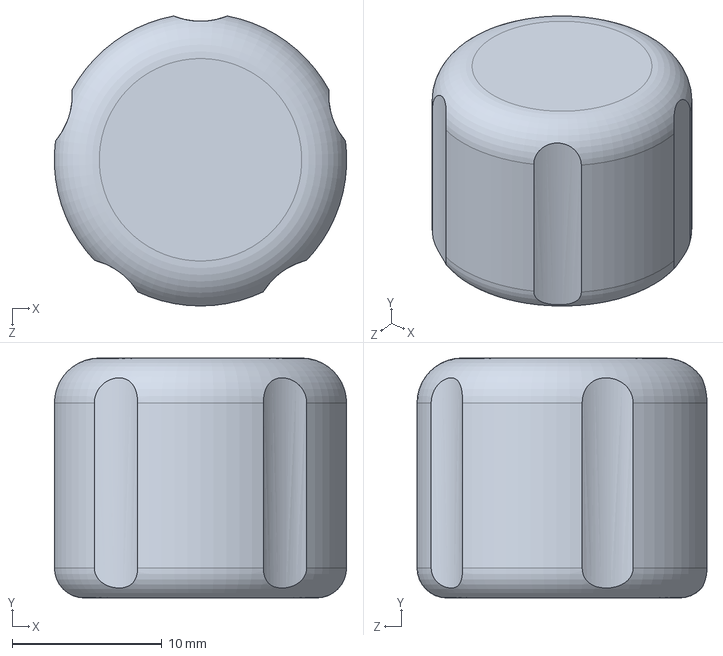
[picture p47: CAD file, 2015-11-12]
Hardware/Enclosure/Slotted_Knob1.SLDPRT
19.5 x 16.0 x 19.3 mm
