MichaelRColton/PSDR/Hardware/Enclosure/7x3x3 Bearing.SLDPRT

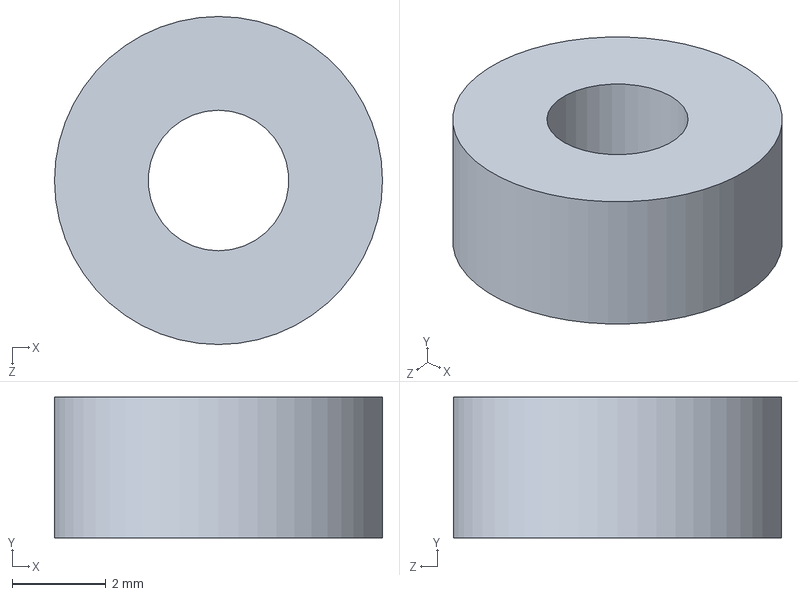
[picture p48: CAD file, 2015-11-12]
Hardware/Enclosure/7x3x3 Bearing.SLDPRT
7.00 x 3.00 x 7.00 mm
