MichaelRColton/PSDR/Hardware/Enclosure/BNC_Adapter.SLDPRT

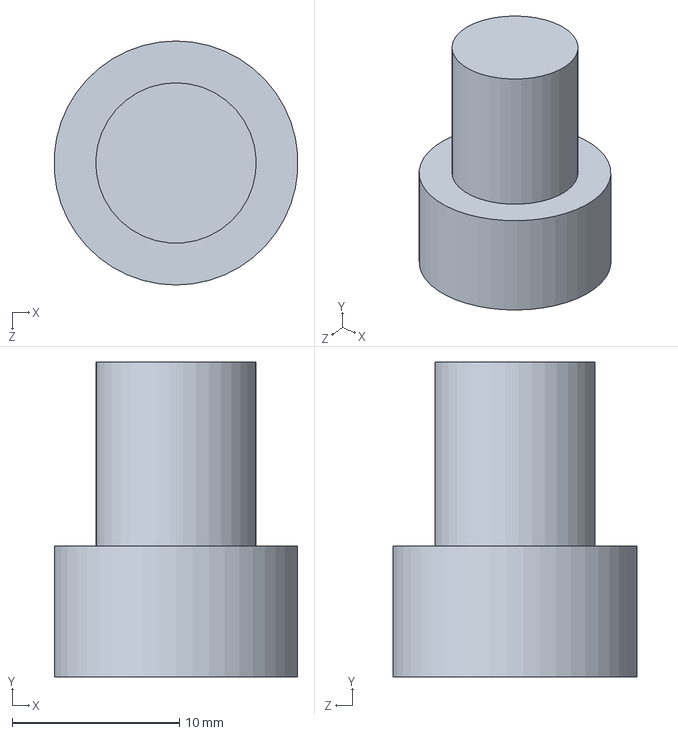
[picture p49: CAD file, 2014-10-28]
Hardware/Enclosure/BNC_Adapter.SLDPRT
14.6 x 18.9 x 14.6 mm
