MichaelRColton/PSDR/Keychain/Assembly.png

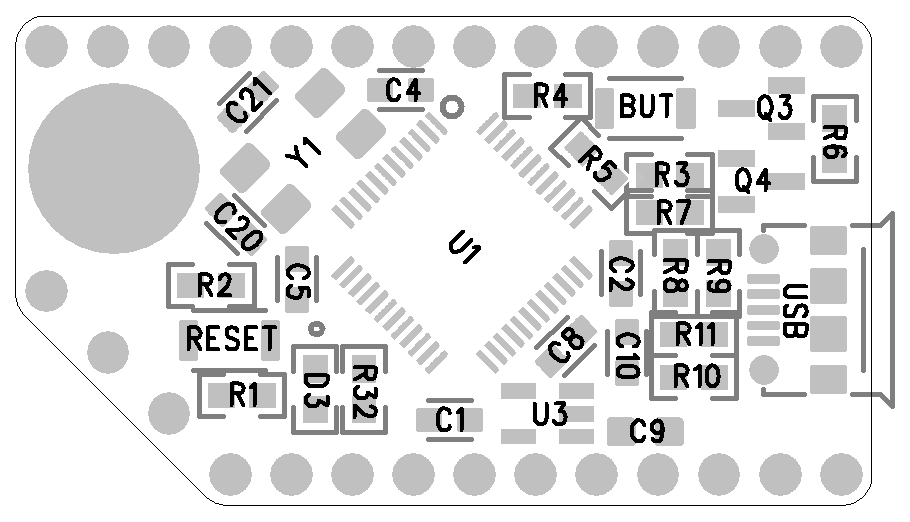
Keychain/Assembly.png
