MichaelRColton/PSDR/Hardware/Test Boards/MultiTest2 Gerbers/BOTTOM.png

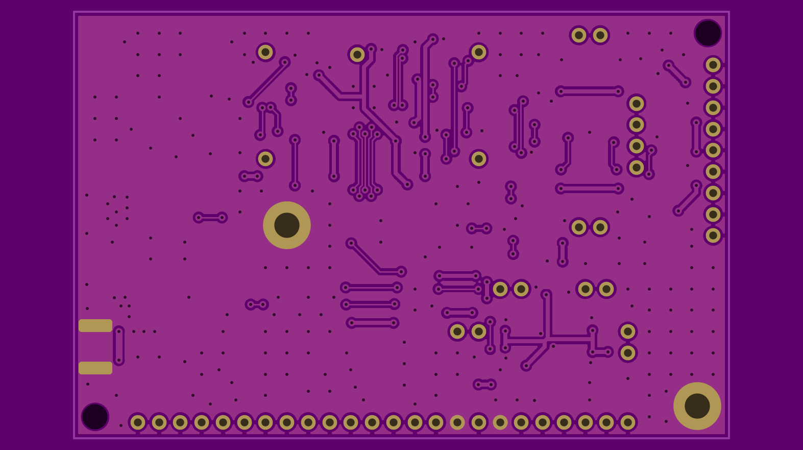
Hardware/Test Boards/MultiTest2 Gerbers/BOTTOM.png
