MichaelRColton/PSDR/Hardware/Test Boards/MultiTest2 Gerbers/TOP.png

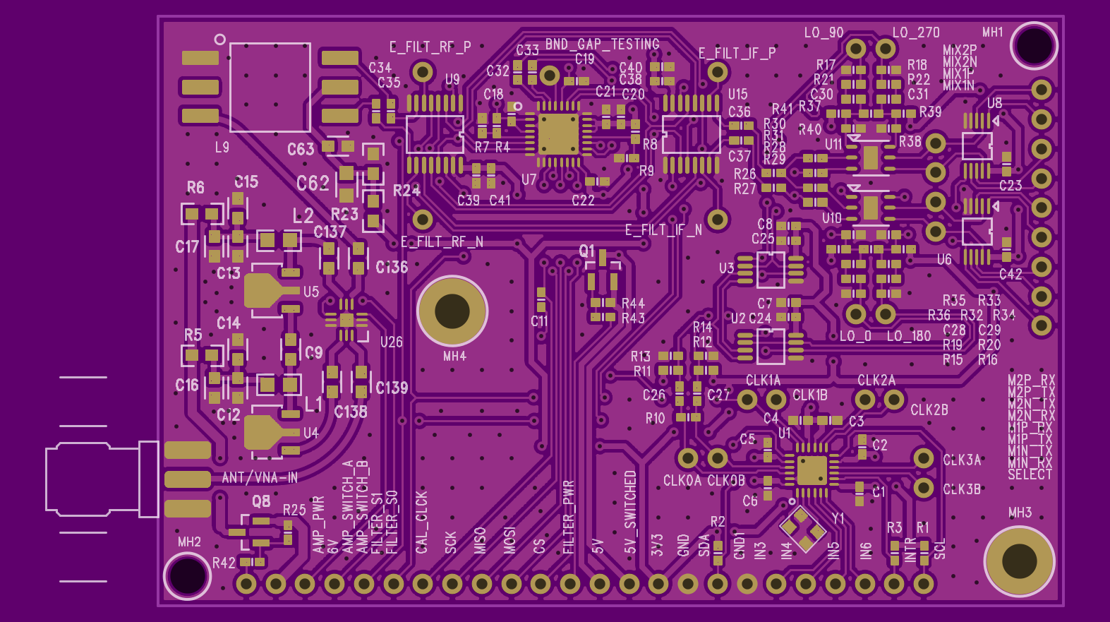
Hardware/Test Boards/MultiTest2 Gerbers/TOP.png
