MichaelRColton/PSDR/Source/src/i2c.c

#include <i2c.h>




HAL_I2C_MspInit(I2C_HandleTypeDef hi2c)
{
  //Ensure that appropriate GPIO and I2C hardware is powered up
  //um, they are elsewhere. Good enough for now.

  //handleI2C = &hi2c;

 GPIO_InitTypeDef gpioInitStructure;


 //Check for stuck SDA condition and attempt to clear it
//  gpioInitStructure.Pin = I2C_SDA.pin;
//  gpioInitStructure.Speed = GPIO_SPEED_FAST;
//  gpioInitStructure.Mode = GPIO_MODE_OUTPUT_OD;
//  gpioInitStructure.Pull = GPIO_PULLUP;
//  gpioInitStructure.Alternate = 0;
//  HAL_GPIO_Init (I2C_SDA.port, &gpioInitStructure);
//
//
//  gpioInitStructure.Pin = I2C_SCL.pin;
//  gpioInitStructure.Speed = GPIO_SPEED_FAST;
//  gpioInitStructure.Mode = GPIO_MODE_OUTPUT_OD;
//  gpioInitStructure.Pull = GPIO_PULLUP;
//  gpioInitStructure.Alternate = 0;
//  HAL_GPIO_Init (I2C_SCL.port, &gpioInitStructure);
//
//
//
//  //Attempt to clear stuck SDA state (caused by poorly timed reset, for example)
//  int retries = 0;
//  //while((!HAL_GPIO_ReadPin(I2C_SDA.port, I2C_SDA.pin)) && retries < 100)
//    while(retries < 10)
//    {
//      HAL_GPIO_WritePin(I2C_SCL.port, I2C_SCL.pin, 0);
//      HAL_GPIO_WritePin(I2C_SCL.port, I2C_SCL.pin, 1);
//      retries++;
//    }
//
//    HAL_GPIO_WritePin(I2C_SDA.port, I2C_SDA.pin, 1);
//    HAL_GPIO_WritePin(I2C_SCL.port, I2C_SCL.pin, 0);
//    HAL_GPIO_WritePin(I2C_SDA.port, I2C_SDA.pin, 0);


 //THESE HAVE TO BE SET UP IN THIS ORDER!! If they are flipped, the BUSY flag will get flipped and never clear and you'll have a bad day.
  gpioInitStructure.Pin = I2C_SCL.pin;
  gpioInitStructure.Speed = GPIO_SPEED_FAST;
  gpioInitStructure.Mode = GPIO_MODE_AF_OD;
  gpioInitStructure.Pull = GPIO_PULLUP;
  gpioInitStructure.Alternate = GPIO_AF4_I2C2;
  HAL_GPIO_Init (I2C_SCL.port, &gpioInitStructure);

 gpioInitStructure.Pin = I2C_SDA.pin;
  gpioInitStructure.Speed = GPIO_SPEED_FAST;
  gpioInitStructure.Mode = GPIO_MODE_AF_OD;
  gpioInitStructure.Pull = GPIO_PULLUP;
  gpioInitStructure.Alternate = GPIO_AF4_I2C2;
  HAL_GPIO_Init (I2C_SDA.port, &gpioInitStructure);



//  (*hi2c).Init.AddressingMode = I2C_ADDRESSINGMODE_7BIT;
//  (*hi2c).Init.ClockSpeed = I2C_
}


clearStuckBusyFlag()
{
  //disable I2C peripheral
  //__I2C2_CLK_DISABLE();
  I2C2->CR1 &= 0b1111111111111110;

  //set pins as OD high,
  GPIO_InitTypeDef gpioInitStructure;
    gpioInitStructure.Pin = I2C_SDA.pin;
    gpioInitStructure.Speed = GPIO_SPEED_FAST;
    gpioInitStructure.Mode = GPIO_MODE_OUTPUT_OD;
    gpioInitStructure.Pull = GPIO_NOPULL;
    gpioInitStructure.Alternate = 0;
    HAL_GPIO_Init (I2C_SDA.port, &gpioInitStructure);

    gpioInitStructure.Pin = I2C_SCL.pin;
    gpioInitStructure.Speed = GPIO_SPEED_FAST;
    gpioInitStructure.Mode = GPIO_MODE_OUTPUT_OD;
    gpioInitStructure.Pull = GPIO_NOPULL;
    gpioInitStructure.Alternate = 0;
    HAL_GPIO_Init (I2C_SCL.port, &gpioInitStructure);

    HAL_GPIO_WritePin(I2C_SCL.port, I2C_SCL.pin, 1);
    HAL_GPIO_WritePin(I2C_SDA.port, I2C_SDA.pin, 1);

  //set them low (and check them)
    HAL_GPIO_WritePin(I2C_SCL.port, I2C_SCL.pin, 0);
    HAL_GPIO_WritePin(I2C_SDA.port, I2C_SDA.pin, 0);

  //set them high (and check them)
    HAL_GPIO_WritePin(I2C_SCL.port, I2C_SCL.pin, 1);
    HAL_GPIO_WritePin(I2C_SDA.port, I2C_SDA.pin, 1);

  //return pins to AF configuration
    gpioInitStructure.Pin = I2C_SDA.pin;
    gpioInitStructure.Speed = GPIO_SPEED_FAST;
    gpioInitStructure.Mode = GPIO_MODE_AF_OD;
    gpioInitStructure.Pull = GPIO_PULLUP;
    gpioInitStructure.Alternate = GPIO_AF4_I2C2;
    HAL_GPIO_Init (I2C_SDA.port, &gpioInitStructure);

    gpioInitStructure.Pin = I2C_SCL.pin;
    gpioInitStructure.Speed = GPIO_SPEED_FAST;
    gpioInitStructure.Mode = GPIO_MODE_AF_OD;
    gpioInitStructure.Pull = GPIO_PULLUP;
    gpioInitStructure.Alternate = GPIO_AF4_I2C2;
    HAL_GPIO_Init (I2C_SCL.port, &gpioInitStructure);

  //set the reset bit in I2Cx_CR1 register then clear it
    I2C2->CR1 |= 0b1000000000000000;
    I2C2->CR1 &= 0b0111111111111111;

  //turn I2C peripheral back on
    //__I2C2_CLK_ENABLE();
    I2C2->CR1 |= 0b0000000000000001;
}




#define NUM_REGS_MAX 350
#define SI5338_ADDRESS 0x70
#define LOCK_MASK 0x15
#define LOS_MASK 0x04



//typedef struct Reg_Data{
//   unsigned unsigned char Reg_Addr;
//   unsigned unsigned char Reg_Val;
//   unsigned unsigned char Reg_Mask;
//} Reg_Data;

//Reg_Data const code Reg_Store[NUM_REGS_MAX] = {
unsigned char Reg_Store[][3] = {
    {  0,0x00,0x00},
    {  1,0x00,0x00},
    {  2,0x00,0x00},
    {  3,0x00,0x00},
    {  4,0x00,0x00},
    {  5,0x00,0x00},
    {  6,0x08,0x1D},
    {  7,0x00,0x00},
    {  8,0x70,0x00},
    {  9,0x0F,0x00},
    { 10,0x00,0x00},
    { 11,0x00,0x00},
    { 12,0x00,0x00},
    { 13,0x00,0x00},
    { 14,0x00,0x00},
    { 15,0x00,0x00},
    { 16,0x00,0x00},
    { 17,0x00,0x00},
    { 18,0x00,0x00},
    { 19,0x00,0x00},
    { 20,0x00,0x00},
    { 21,0x00,0x00},
    { 22,0x00,0x00},
    { 23,0x00,0x00},
    { 24,0x00,0x00},
    { 25,0x00,0x00},
    { 26,0x00,0x00},
    { 27,0x70,0x80},
    { 28,0x16,0xFF},
    { 29,0x90,0xFF},
    { 30,0xB0,0xFF},
    { 31,0xC0,0xFF},
    { 32,0xC0,0xFF},
    { 33,0xCC,0xFF},
    { 34,0xE3,0xFF},
    { 35,0x00,0xFF},
    { 36,0x06,0x1F},
    { 37,0x06,0x1F},
    { 38,0x06,0x1F},
    { 39,0x00,0x1F},
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
    {255, 1, 0xFF}, // set page bit to 1
    {  0,0x00,0x00},
    {  1,0x00,0x00},
    {  2,0x00,0x00},
    {  3,0x00,0x00},
    {  4,0x00,0x00},
    {  5,0x00,0x00},
    {  6,0x00,0x00},
    {  7,0x00,0x00},
    {  8,0x00,0x00},
    {  9,0x00,0x00},
    { 10,0x00,0x00},
    { 11,0x00,0x00},
    { 12,0x00,0x00},
    { 13,0x00,0x00},
    { 14,0x00,0x00},
    { 15,0x00,0x00},
    { 16,0x00,0x00},
    { 17,0x01,0x00},
    { 18,0x00,0x00},
    { 19,0x00,0x00},
    { 20,0x90,0x00},
    { 21,0x31,0x00},
    { 22,0x00,0x00},
    { 23,0x00,0x00},
    { 24,0x01,0x00},
    { 25,0x00,0x00},
    { 26,0x00,0x00},
    { 27,0x00,0x00},
    { 28,0x00,0x00},
    { 29,0x00,0x00},
    { 30,0x00,0x00},
    { 31,0x00,0xFF},
    { 32,0x00,0xFF},
    { 33,0x01,0xFF},
    { 34,0x00,0xFF},
    { 35,0x00,0xFF},
    { 36,0x90,0xFF},
    { 37,0x31,0xFF},
    { 38,0x00,0xFF},
    { 39,0x00,0xFF},
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



unsigned char hello = 1;

void write_Si5338(unsigned char address, unsigned char value)
{
  unsigned char txBuf[2];
  txBuf[0] = address;
  txBuf[1] = value;

  HAL_I2C_Master_Transmit(&handleI2C, 0xE0, &txBuf, 2, 100);
  //HAL_I2C_Mem_Write(&handleI2C, 0xE0, address, 1, value, 1, 100);

//  Wire.beginTransmission(SI5338_ADDRESS);
//  Wire.write(address);
//  //delay(10);
//  Wire.write(value);
//  Wire.endTransmission();
//  delay(10);
//  Serial.print(address, DEC);
//  Serial.print(" w ");
//  Serial.print(value, DEC);
//  Serial.print("\r\n");
}

#define MULTISYNTH0 53
void writeMultiSynthParameters(int multisynth, unsigned long a, unsigned long b, unsigned long c)
{
  unsigned long long msx_p1 = ((a * c + b) * 128) / c - 512;
  unsigned long long msx_p2 = (b * 128) % c;
  unsigned long long msx_p3 = c;

  write_Si5338(multisynth,     ( msx_p1 & 0xFF));
  write_Si5338(multisynth + 1, ( msx_p1 >> 8) & 0xFF);
  write_Si5338(multisynth + 2, (( msx_p1 >> 16) & 0b00000011) + (( msx_p2 << 2 ) & 0b11111100));
  write_Si5338(multisynth + 3, ( msx_p2 >> 6 ) & 0xFF);
  write_Si5338(multisynth + 4, ( msx_p2 >> 14 ) & 0xFF);
  write_Si5338(multisynth + 5, ( msx_p2 >> 22 ) & 0xFF);
  write_Si5338(multisynth + 6, ( msx_p3 & 0xFF));
  write_Si5338(multisynth + 7, ( msx_p3 >> 8) & 0xFF);
  write_Si5338(multisynth + 8, ( msx_p3 >> 16) & 0xFF);
  write_Si5338(multisynth + 9, ( msx_p3 >> 24) & 0b00111111);
}

unsigned char read_Si5338(unsigned char address, int increment)
{
  unsigned char retVal = 0;

  HAL_I2C_Master_Transmit(&handleI2C, 0xE0, &address, 1, 100);

  HAL_I2C_Master_Receive(&handleI2C, 0xE0, &retVal, 1, 100);


//  Wire.beginTransmission(SI5338_ADDRESS);
//  //Wire.write(0x00);
//  Wire.write(address);
//  Wire.endTransmission();
//
//  //delay(2);
//  Wire.beginTransmission(SI5338_ADDRESS);
//  Wire.requestFrom(SI5338_ADDRESS,1);
//
//  while(Wire.available())
//  {
//    retVal = Wire.read();
//    delay(10);
//    Serial.print(address, DEC);
//    Serial.print(" r ");
//    Serial.print(retVal, DEC);
//    Serial.print(" - ");
//    Serial.print(Reg_Store[increment][1], DEC);
//    Serial.print("\r\n");
//  }

  return retVal;
}

//add, val, mask
void sendRegToSi5338(int increment)
{
  unsigned char addr = Reg_Store[increment][0];
  unsigned char data = Reg_Store[increment][1];
  unsigned char mask = Reg_Store[increment][2];
//  unsigned char addr = Reg_Store[increment].Reg_Addr;
//  unsigned char data = Reg_Store[increment].Reg_Val;
//  unsigned char mask = Reg_Store[increment].Reg_Mask;

  // ignore registers with masks of 0x00
  if(mask != 0x00){
    if(mask == 0xFF){
      // do a regular I2C write to the register
      // at addr with the desired data value
      write_Si5338(addr, data);
    } else {
      // do a read-modify-write using I2C and
      // bit-wise operations
      // get the current value from the device at the
      // register located at addr
      unsigned char curr_val = read_Si5338(addr, increment);
      // clear the bits that are allowed to be
      // accessed in the current value of the register
      unsigned char clear_curr_val = curr_val & (~ mask);
      // clear the bits in the desired data that
      // are not allowed to be accessed
      unsigned char clear_new_val = data & mask;
      // combine the cleared values to get the new
      // value to write to the desired register
      unsigned char combined = clear_curr_val | clear_new_val;
      write_Si5338(addr, combined);
    }
  } else {
    //Serial.println("skip");
  }
}


void i2cSetup() {
  // put your setup code here, to run once:

  //pinMode(A3, INPUT);
  //digitalWrite(A3, LOW);


  //Serial.begin(115200);
  //Serial.write("\n\r\n\rHi Michael, you can do this\n\r");
  //Wire.begin();

//delay(50);

////This part is working correctly!
//  for(int i = 0; i < NUM_REGS_MAX; i++)
//  {
//    Serial.println(Reg_Store[i][1], HEX);
//  }

//Serial.println("and now this part");



//Serial.println("and now THIS part");
  //delay(2000);

  //write_Si5338(230, 1 << 4);
  //write_Si5338(241, 1 << 7);
write_Si5338(230, 0x10); //OEB_ALL = 1
write_Si5338(241, 0xE5); //DIS_LOL = 1

//delay(100);
  for(int i = 0; i < NUM_REGS_MAX; i++)
  {
    sendRegToSi5338(i);
  }
//for(int counter=0; counter<NUM_REGS_MAX; counter++){
//unsigned char curr = Reg_Store[counter];
//if(curr.Reg_Mask != 0x00) {
//  if(curr.Reg_Mask == 0xFF) {
//    // do a write transaction only
//    // since the mask is all ones
//    I2C_ByteWrite(curr.Reg_Addr, curr.Reg_Val);
//  } else {
//    //do a read-modify-write
//    curr_chip_val = I2C_ByteRead(curr.Reg_Addr);
//    clear_curr_val = curr_chip_val & ~curr.Reg_Mask;
//    clear_new_val = curr.Reg_Val & curr.Reg_Mask;
//    combined = clear_new_val | clear_curr_val;
//    I2C_ByteWrite(curr.Reg_Addr, combined);
//    }
//  }
//}

//  write_Si5338(49, 0 << 7);
//  write_Si5338(246, 1 << 1);

//  delay(30);

//  write_Si5338(241, 0 << 7);
//  //skipped some steps
//
//  write_Si5338(230, 0 << 4);

// check LOS alarm for the xtal input
// on IN1 and IN2 (and IN3 if necessary) -
// change this mask if using inputs on IN4, IN5, IN6
unsigned char reg = read_Si5338(218,1) & LOS_MASK;
while(reg != 0){
  reg = read_Si5338(218, 1) & LOS_MASK;
}
//delay(100);
write_Si5338(49, read_Si5338(49,1) & 0x7F); //FCAL_OVRD_EN = 0
write_Si5338(246, 2); //soft reset
write_Si5338(241, 0x65); //DIS_LOL = 0

// wait for Si5338 to be ready after calibration (ie, soft reset)
//delay(50);
//make sure the device locked by checking PLL_LOL and SYS_CAL
reg = read_Si5338(218,1) & LOCK_MASK;
while(reg != 0){
  reg = read_Si5338(218,1) & LOCK_MASK;
}
//delay(100);
//copy FCAL values
write_Si5338(45, read_Si5338(235,1));
write_Si5338(46, read_Si5338(236,1));
// clear bits 0 and 1 from 47 and
// combine with bits 0 and 1 from 237
reg = (read_Si5338(47,1) & 0xFC) | (read_Si5338(237,1) & 3);
write_Si5338(47, reg);
write_Si5338(49, read_Si5338(49,1) | 0x80); // FCAL_OVRD_EN = 1
write_Si5338(230, 0x00); // OEB_ALL = 0

//Serial.println("and that's it");

//  for(int i = 0; i < NUM_REGS_MAX; i++)
//  {
//    read_Si5338(i, i);
//
//  }

//while(1);



write_Si5338(31, 0xC1); //output driver off?

//Start us at a known frequency (in this case 14.06 which equals 7.03)
//TODO: Make this start at whatever the unit is supposed to power up at. Not hard coded
writeMultiSynthParameters(MULTISYNTH0, 201, 697, 703);
write_Si5338(31, 0xC0); //output driver off?
}


unsigned long long vcoFreq = 2840000000;
double correctionFactor = 1;
void setFreq(unsigned long frequency)
{
//void i2cLoop() {
  // put your main code here, to run repeatedly:
  //delay(400);
  //write_Si5338(31, 0xC1); //output driver off?

//long integer = 8;
//long neumerator = 0;
//do
//{
//
//  writeMultiSynthParameters(MULTISYNTH0, integer, neumerator, 10000UL);
//  //neumerator += 1000;
//  //if(neumerator > 9999)
//  //{
//  //  neumerator = 0;
//    integer++;
//
//  //}
//  if( integer >= 500) integer = 8;
//
//} while (true);
//double  desiredFrequency = 150.5;
//double  measuredFrequency = 150.48806;


//  correctionFactor = desiredFrequency/measuredFrequency;

//  frequency *= correctionFactor;

  frequency *= 2; //because the flipflops will devide it back down by 2

if(frequency < 5000000) return;
if(frequency > 350000000) return;



unsigned long integer = vcoFreq / frequency;

//if((integer % 2) != 0) integer++;



unsigned long remainder = vcoFreq % frequency;


//do
//{

  //writeMultiSynthParameters(MULTISYNTH0, integer, neumerator, 10000UL);
  //neumerator += 1000;
  //if(neumerator > 9999)
  //{
  //  neumerator = 0;
  //  integer++;

  //}
//  if( integer >= 500) integer = 8;

  //neumerator = (analogRead(A3) * 10); //578914 referal nu  801 435 7764 john thank you
  //integer = (analogRead(A2) /10) + 150;
//
//} while (true);


    //write_Si5338(31, 0xC0); //output driver off?

  //delay(400);



while(frequency > 100000) //This value should be fine tuned. I thought the numerator and denominator could be 30 bits, but it seems to be less than 24
  {
    remainder /= 2;
    frequency /= 2;
  }

    //write_Si5338(31, 0xC1); //output driver off?
    writeMultiSynthParameters(MULTISYNTH0, integer, remainder , frequency);
    //writeMultiSynthParameters(MULTISYNTH0, 232, 44960 , 122220);
  //writeMultiSynthParameters(MULTISYNTH0, integer, /*neumerator*/ 0 , 1000000UL);
    //write_Si5338(31, 0xC0); //output driver off?

}
