MichaelRColton/PSDR/Source/src/images.c

#include "images.h"

//This site seems to generate output that is correct
//http://www.rinkydinkelectronics.com/t_imageconverter565.php
//BUT it will round down to the nearest 16 words, so you need to pad the image, and then delete the excess!!

//I don't remember what font I used. Something that was on my work computer,
//and I don't think there are too many extra fonts installed on it. I'll figure it out later.
//Looks like it's Aerial Black. The mode icon's are 9pt.

//Also, I wonder if I want to encode the height and width in the first two bytes or something? That seems like that's not a bad idea.

//86x20
const const unsigned short psdrLogo[]={
		0x0000, 0x0000, 0x0000, 0x0000, 0x0000, 0x0000, 0x0000, 0x0336, 0xFFFF, 0xFFFF, 0xFFFF, 0xFFFF, 0xFFFF, 0xFFFF, 0xFFFF, 0xFFFF,   // 0x0010 (16) pixels
		0xFFFF, 0xFFFF, 0xFFFF, 0xFFFF, 0xFFF6, 0x6000, 0x0000, 0x0000, 0x0000, 0x0000, 0x0000, 0x0000, 0x0000, 0x0000, 0x0000, 0x0336,   // 0x0020 (32) pixels
		0xFFFF, 0xFFFF, 0xFFFF, 0xFFFF, 0xFFFF, 0xFFFF, 0xFFFF, 0xFDAC, 0x0000, 0x0000, 0x0000, 0x0000, 0x0000, 0x0000, 0x0000, 0x0336,   // 0x0030 (48) pixels
		0xFFFF, 0xFFFF, 0xFFFF, 0xFFFF, 0xFFFF, 0xFFFF, 0xFFFF, 0xFFFF, 0xFFFF, 0xFFFF, 0xFFFF, 0xFFFB, 0x91C0, 0x0000, 0x0000, 0x0000,   // 0x0040 (64) pixels
		0x0000, 0x0000, 0x0000, 0x0000, 0x0336, 0xFFFF, 0xFFFF, 0xFFFF, 0xFFFF, 0xFFFF, 0xFFFF, 0xFFFF, 0xFFFF, 0xFFFF, 0xFFFF, 0xFFFF,   // 0x0050 (80) pixels
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
		0x0000, 0x0000, 0x0000, 0x0000, 0x0000, 0x0000, 0x0000, 0x0000, 0x0000, 0x0000, 0x0000, 0x0000, 0x0000, 0x0000, 0x0000, 0x0000,   // 0x0040 (64) pixels
		0x0000, 0x0000, 0x0000, 0x0000, 0x0000, 0x0000, 0x0000, 0x0000};

const unsigned short tildeSmall[] ={
		0x0000, 0x0000, 0x0000, 0x0000, 0x0000, 0x0000, 0x0000, 0x0000, 0x0000, 0x0000, 0x0000, 0x0000, 0x0000, 0x0000, 0x0000, 0x0000,   // 0x0010 (16) pixels
		0x0000, 0x0000, 0x0000, 0x0000, 0x0000, 0x0000, 0x0000, 0x0000, 0x000A, 0xA71F, 0xFFFF, 0xFFFC, 0xA2A0, 0x0000, 0x0418, 0xC400,   // 0x0020 (32) pixels
		0x553C, 0xFFFF, 0xFFFF, 0xFFFF, 0xFFFF, 0xFFFF, 0xFFFF, 0xC400, 0x5538, 0xA2A0, 0x0000, 0x02B4, 0xE7FF, 0xFFFF, 0xFE30, 0x0000,   // 0x0030 (48) pixels
		0x0000, 0x0000, 0x0000, 0x0000, 0x0000, 0x0000, 0x0000, 0x0000, 0x0000, 0x0000, 0x0000, 0x0000, 0x0000, 0x0000, 0x0000, 0x0000,   // 0x0040 (64) pixels
		0x0000, 0x0000, 0x0000, 0x0000, 0x0000, 0x0000, 0x0000, 0x0000};
