MichaelRColton/PSDR/Source/include/images.h

/*
 * BMP image data converted from 24bpp
 * to RGB565
 */

#define COLOR_BPP          16
#define COLOR_STORAGE_SIZE 2
#define BMPWIDTH           69;
#define BMPHEIGHT          33;

extern const unsigned short psdrLogo[];
extern const unsigned short bitmapMode[];
extern const unsigned short bitmapLSB[];
extern const unsigned short bitmapUSB[];
extern const unsigned short bitmapAM[];
extern const unsigned short bitmapPeriod[];
extern const unsigned short bitmapOne[];
extern const unsigned short bitmapTwo[];
extern const unsigned short bitmapThree[];
extern const unsigned short bitmapFour[];
extern const unsigned short bitmapFive[];
extern const unsigned short bitmapSix[];
extern const unsigned short bitmapSeven[];
extern const unsigned short bitmapEight[];
extern const unsigned short bitmapNine[];
extern const unsigned short bitmapZero[];
extern const unsigned short bitmapIronGradient[];
extern const unsigned short bitmapWebSdrGradient[];
extern const unsigned short bitmapFilter[];
extern const unsigned short bitmapHadLogo[];
extern const unsigned short bitmapSMeter[];

const unsigned short oneSmall[];
const unsigned short twoSmall[];
const unsigned short threeSmall[];
const unsigned short fourSmall[];
const unsigned short fiveSmall[];
const unsigned short sixSmall[];
const unsigned short sevenSmall[];
const unsigned short eightSmall[];
const unsigned short nineSmall[];
const unsigned short zeroSmall[];
const unsigned short hyphenSmall[];
const unsigned short tildeSmall[];
